oliverpaddock/OpenMic/hardware/sims/output.asc

B1: bv; V=white(2.8e6*time)*0.0038
B2: bv; V=white(45e6*time)*0.005
B3: bv; V=white(8.4e6*time)*0.000021
B4: bv; V=white(8.4e6*time)*0.000021
B5: bv; V=white(2e6*time)*0.000002
C1: Cap; 47µ
C2: Cap; 100n
C3: Cap; 100n
C4: Cap; 100n
C5: Cap; 100n
C6: Cap; 47µ
R1: Res; 10
R2: Res; 1k
R3: Res; 5k1
R4: Res; 1k
R5: Res; 10
R6: Res; 1k
R8: Res; 6.34k
R9: Res; 6.34k
R11: Res; 1k
U1: opamp2; OPA161x
U2: OPA1637
V1: Voltage; 48
V2: Voltage; SINE(0 3.8m 700k 0 0 0)
V3: Voltage; 3.3
V4: Voltage; SINE(0 5m 2.25meg)
V5: Voltage; 15.2
V6: Voltage; SINE(0 5m 420k)
V7: Voltage; -15.1
V8: Voltage; SINE(0 5m 420k)
V9: Voltage; 2.75
V10: Voltage; SINE(1.65 .5 440); AC 1; Cpar=2n
V11: Voltage; SINE(1.65 .5 440); AC 1; Cpar=2n
Named nets: 0, +48V_PH, +3V3, +15V, -15V, +2V75_BIAS
.lib ./models/OPA161x.lib
.lib ./models/OPA1622.lib
.lib ./models/OPA1637.lib
.lib ./models/OPA164x.lib
.lib ./models/OPA1656.lib
.lib ./models/THAT120x.lib
.lib ./models/THAT1580.lib
.lib ./models/THAT5173.lib
.tran 0 5m
