oliverpaddock/OpenMic/hardware/pcb/prototypes/input/v1/input.kicad_pcb

## KiCad design hardware/pcb/prototypes/input/v1/input.kicad_pcb (2026-06-01, an earlier design)

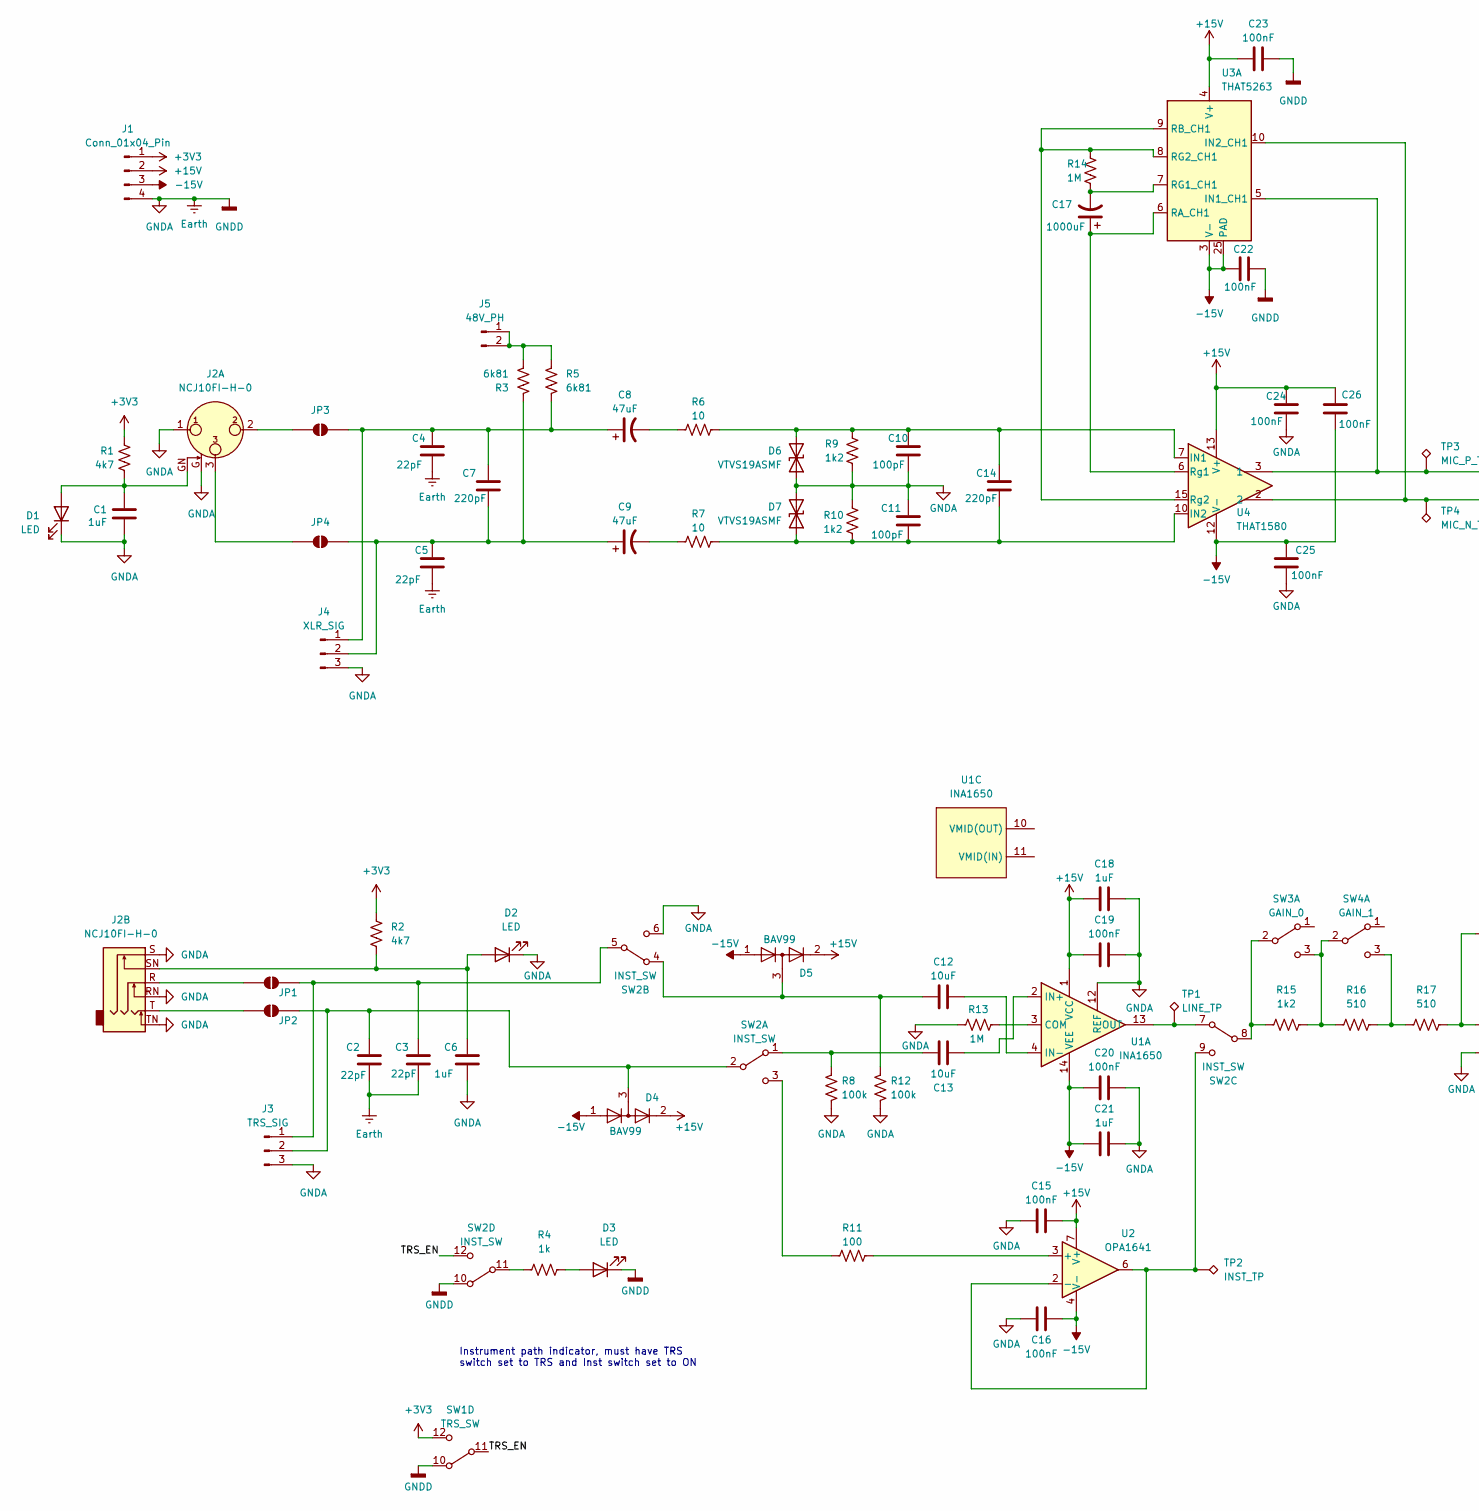
[picture p43: schematic input.kicad_sch, Audio input test, part in row 1, column 1]

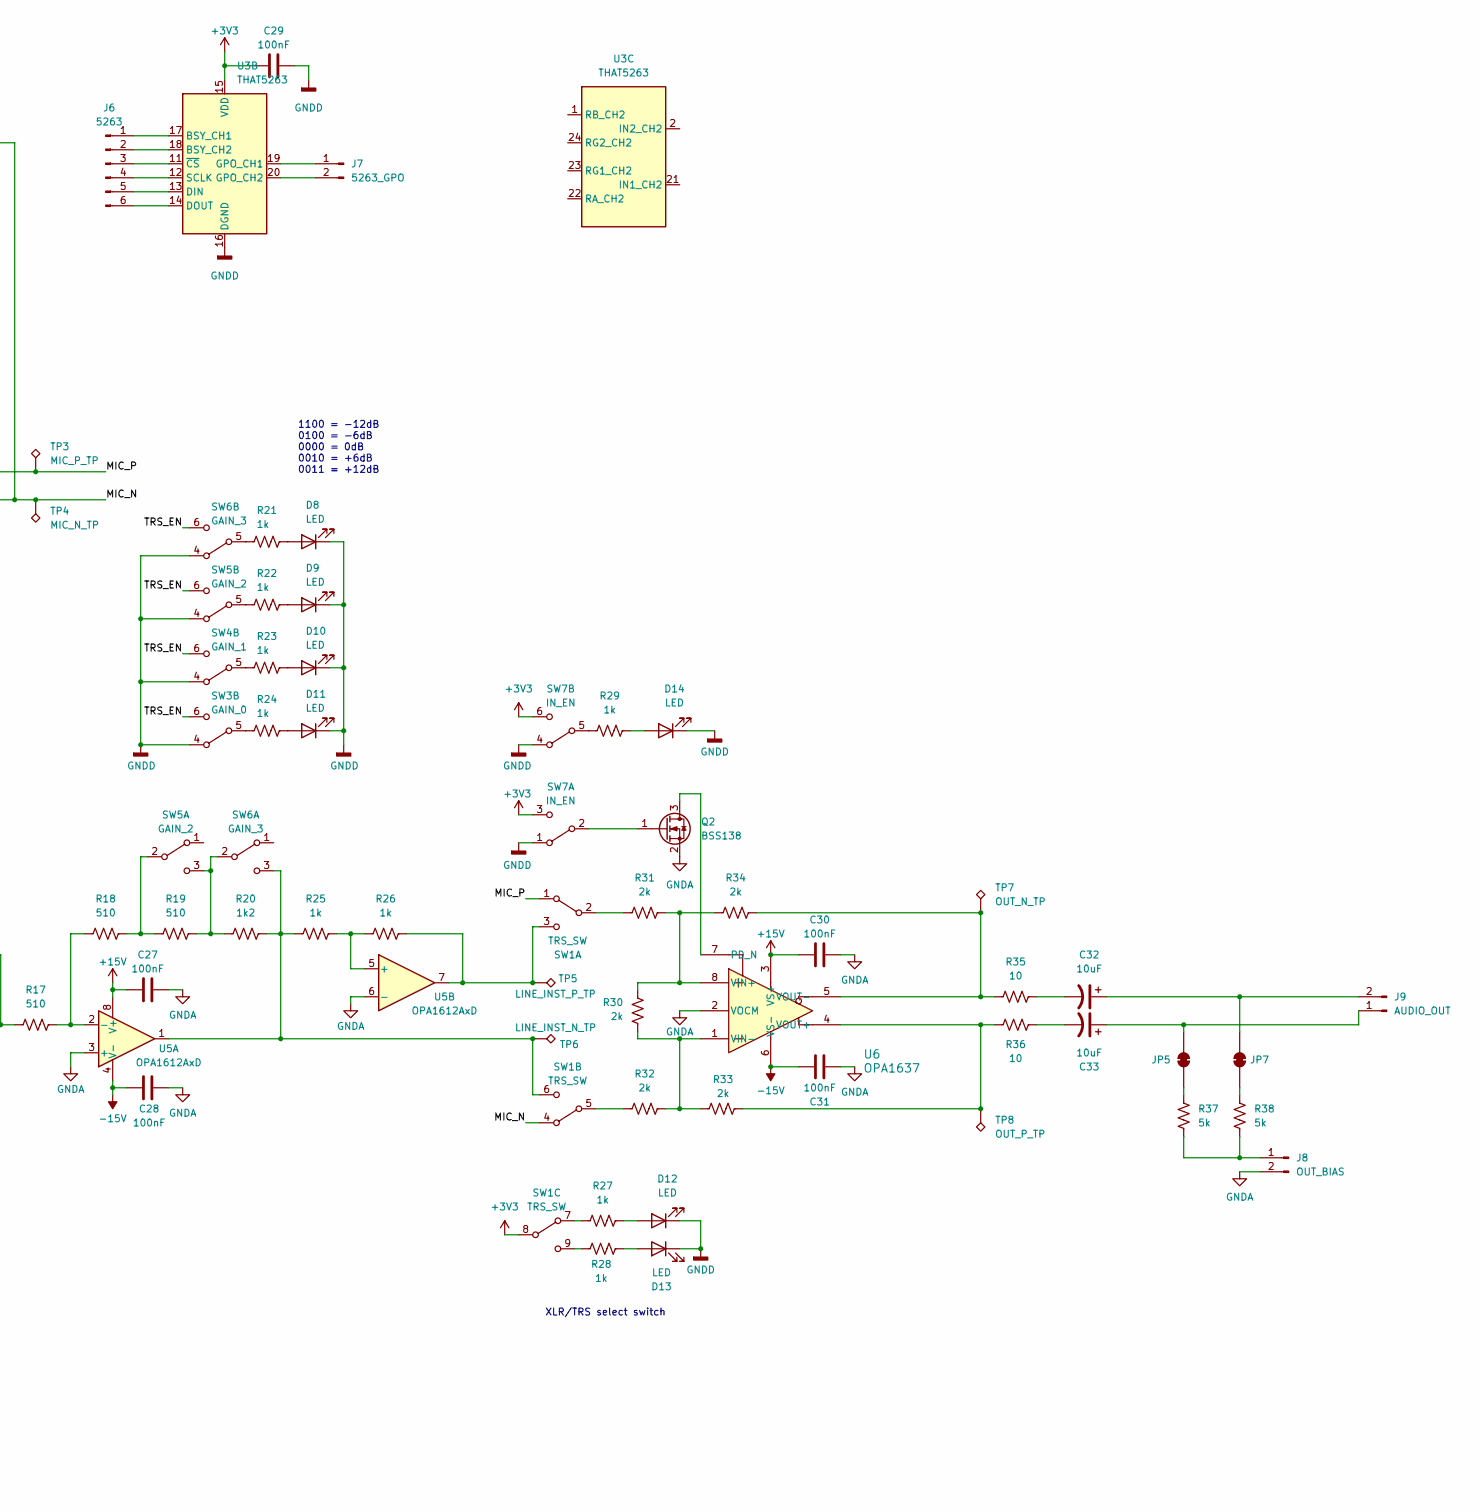
[picture p44: schematic input.kicad_sch, Audio input test, part in row 1, column 2]

Parts:
C1, C6, C18, C21: 1uF; C_0805_2012Metric_Pad1.18x1.45mm_HandSolder
C2, C3, C4, C5: 22pF; C_0805_2012Metric_Pad1.18x1.45mm_HandSolder
C7, C14: 220pF; C_0805_2012Metric_Pad1.18x1.45mm_HandSolder
C8, C9: 47uF; CP_Elec_6.3x5.8
C10, C11: 100pF; C_0805_2012Metric_Pad1.18x1.45mm_HandSolder
C12, C13: 10uF; C_0805_2012Metric_Pad1.18x1.45mm_HandSolder
C15, C16, C19, C20, C22, C23, C24, C25, C26, C27, C28, C29, C30, C31: 100nF; C_0805_2012Metric_Pad1.18x1.45mm_HandSolder
C17: 1000uF; CP_Elec_8x10
C32, C33: 10uF; CP_Elec_5x5.4
D1, D2, D3, D8, D9, D10, D11, D12, D13, D14: LED; LED_0805_2012Metric_Pad1.15x1.40mm_HandSolder
D4, D5: BAV99; TSOT-23_HandSoldering
D6, D7: VTVS19ASMF; D_SMF
J1: Conn_01x04_Pin; PinHeader_1x04_P2.54mm_Vertical
J2: NCJ10FI-H-0; Jack_XLR-6.35mm_Neutrik_NCJ10FI-H-0_Horizontal
J3: TRS_SIG; PinHeader_1x03_P2.54mm_Vertical
J4: XLR_SIG; PinHeader_1x03_P2.54mm_Vertical
J5: 48V_PH; PinHeader_1x02_P2.54mm_Vertical
J6: 5263; PinHeader_1x06_P2.54mm_Vertical
J7: 5263_GPO; PinHeader_1x02_P2.54mm_Vertical
J8: OUT_BIAS; PinHeader_1x02_P2.54mm_Vertical
J9: AUDIO_OUT; PinHeader_1x02_P2.54mm_Vertical
JP1, JP2, JP3, JP4: SolderJumper_2_Open; SolderJumper-2_P1.3mm_Open_RoundedPad1.0x1.5mm
JP5, JP7: SolderJumper_2_Bridged; SolderJumper-2_P1.3mm_Bridged2Bar_RoundedPad1.0x1.5mm
Q2: BSS138; SOT-23
R1, R2: 4k7; R_0805_2012Metric_Pad1.20x1.40mm_HandSolder
R3, R5: 6k81; R_0805_2012Metric_Pad1.20x1.40mm_HandSolder
R4, R21, R22, R23, R24, R25, R26, R27, R28, R29: 1k; R_0805_2012Metric_Pad1.20x1.40mm_HandSolder
R6, R7, R35, R36: 10; R_0805_2012Metric_Pad1.20x1.40mm_HandSolder
R8, R12: 100k; R_0805_2012Metric_Pad1.20x1.40mm_HandSolder
R9, R10, R15, R20: 1k2; R_0805_2012Metric_Pad1.20x1.40mm_HandSolder
R11: 100; R_0805_2012Metric_Pad1.20x1.40mm_HandSolder
R13, R14: 1M; R_0805_2012Metric_Pad1.20x1.40mm_HandSolder
R16, R17, R18, R19: 510; R_0805_2012Metric_Pad1.20x1.40mm_HandSolder
R30, R31, R32, R33, R34: 2k; R_0805_2012Metric_Pad1.20x1.40mm_HandSolder
R37, R38: 5k; R_0805_2012Metric_Pad1.20x1.40mm_HandSolder
SW1: TRS_SW; 4PDT_SW
SW2: INST_SW; 4PDT_SW
SW3: GAIN_0; DPDT_SW
SW4: GAIN_1; DPDT_SW
SW5: GAIN_2; DPDT_SW
SW6: GAIN_3; DPDT_SW
SW7: IN_EN; DPDT_SW
TP1: LINE_TP; TestPoint_Pad_D1.0mm
TP2: INST_TP; TestPoint_Pad_D1.0mm
TP3: MIC_P_TP; TestPoint_Pad_D1.0mm
TP4: MIC_N_TP; TestPoint_Pad_D1.0mm
TP5: LINE_INST_P_TP; TestPoint_Pad_D1.0mm
TP6: LINE_INST_N_TP; TestPoint_Pad_D1.0mm
TP7: OUT_N_TP; TestPoint_Pad_D1.0mm
TP8: OUT_P_TP; TestPoint_Pad_D1.0mm
U1: INA1650; TSSOP-14_4.4x5mm_P0.65mm
U2: OPA1641; SOIC-8_3.9x4.9mm_P1.27mm
U3: THAT5263; QFN-24-1EP_5x5mm_P0.65mm_EP3.4x3.4mm
U4: THAT1580; QFN-16-1EP_4x4mm_P0.65mm_EP2.1x2.1mm_ThermalVias
U5: OPA1612AxD; SOIC-8_3.9x4.9mm_P1.27mm
U6: OPA1637; VSSOP-8_3x3mm_P0.65mm

Connections:
+3V3: C29.1, J1.1, R1.1, R2.1, SW1.8 (B), SW1.12 (C), SW7.3 (C), SW7.6 (C), U3.15 (VDD)
+15V: C15.1, C18.2, C19.2, C23.1, C24.1, C26.1, C27.1, C30.1, D4.2 (A), D5.2 (A), J1.2, U1.1 (VCC), U2.7 (V+), U3.4 (V+), U4.13 (V+), U5.8 (V+), U6.3 (VS+)
-15V: C16.1, C20.1, C21.2, C22.1, C25.1, C26.2, C28.1, C31.1, D4.1 (K), D5.1 (K), J1.3, U1.14 (VEE), U2.4 (V-), U3.3 (V-), U3.25 (PAD), U4.12 (V-), U4.17 (V-), U5.4 (V-), U6.6 (VS-)
/MIC_N: SW1.4 (A), TP4.1 (1_1), U3.10 (IN2_CH1), U4.2
/MIC_P: SW1.1 (A), TP3.1 (1_1), U3.5 (IN1_CH1), U4.3 (1)
/TRS_EN: SW1.11 (B), SW2.12 (C), SW3.6 (C), SW4.6 (C), SW5.6 (C), SW6.6 (C)
Earth: C1.2, C2.2, C3.2, C4.2, C5.2, C6.2, C10.2, C11.1, C15.2, C16.2, C18.1, C19.1, C20.2, C21.1, C22.2, C23.2, C24.2, C25.2, C27.2, C28.2, C29.2, C30.2, C31.2, D1.1 (K), D2.1 (K), D3.1 (K), D6.1 (A1), D7.2 (A2), D8.1 (K), D9.1 (K), D10.1 (K), D11.1 (K), D12.1 (K), D13.1 (K), D14.1 (K), J1.4, J2.1, J2.G, J2.RN, J2.S, J2.TN, J3.3, J4.3, J8.2, Q2.2 (S), R8.2, R9.2, R10.1, R12.2, R13.1, SW1.10 (A), SW2.6 (C), SW2.10 (A), SW3.4 (A), SW4.4 (A), SW5.4 (A), SW6.4 (A), SW7.1 (A), SW7.4 (A), U1.12 (REF), U3.16 (DGND), U5.3 (+), U5.6 (-), U6.2 (VOCM)
unnamed: C8.2, R6.1
unnamed: C9.2, R7.1
unnamed: C32.2, R35.2
unnamed: C33.2, R36.2
unnamed: C1.1, D1.2 (A), J2.GN, R1.2
unnamed: C6.1, D2.2 (A), J2.SN, R2.2
unnamed: D3.2 (A), R4.2
unnamed: C10.1, C14.1, D6.2 (A2), R6.2, R9.1, U4.7 (IN1)
unnamed: C11.2, C14.2, D7.1 (A1), R7.2, R10.2, U4.10 (IN2)
unnamed: D8.2 (A), R21.1
unnamed: D9.2 (A), R22.1
unnamed: D10.2 (A), R23.1
unnamed: D11.2 (A), R24.1
unnamed: D12.2 (A), R27.2
unnamed: D13.2 (A), R28.2
unnamed: D14.2 (A), R29.2
unnamed: C3.1, J3.1, JP1.2 (B), SW2.5 (B)
unnamed: C2.1, D4.3 (K), J3.2, JP2.2 (B), SW2.2 (B)
unnamed: C4.1, C7.1, C8.1, J4.1, JP3.2 (B), R5.2
unnamed: C5.1, C7.2, C9.1, J4.2, JP4.2 (B), R3.1
unnamed: J5.1, J5.2, R3.2, R5.1
unnamed: J6.1, U3.17 (BSY_CH1)
unnamed: J6.2, U3.18 (BSY_CH2)
unnamed: J6.3, U3.11 (~CS)
unnamed: J6.4, U3.12 (SCLK)
unnamed: J6.5, U3.13 (DIN)
unnamed: J6.6, U3.14 (DOUT)
unnamed: J7.1, U3.19 (GPO_CH1)
unnamed: J7.2, U3.20 (GPO_CH2)
unnamed: J8.1, R37.1, R38.1
unnamed: C33.1, J9.1, JP5.2 (B)
unnamed: C32.1, J9.2, JP7.2 (B)
unnamed: J2.R, JP1.1 (A)
unnamed: J2.T, JP2.1 (A)
unnamed: J2.2, JP3.1 (A)
unnamed: J2.3, JP4.1 (A)
unnamed: JP5.1 (A), R37.2
unnamed: JP7.1 (A), R38.2
unnamed: Q2.3 (D), U6.7 (PD_N)
unnamed: Q2.1 (G), SW7.2 (B)
unnamed: R31.1, SW1.2 (B)
unnamed: R26.2, SW1.3 (C), TP5.1 (1_1), U5.7
unnamed: R32.1, SW1.5 (B)
unnamed: R20.2, R25.1, SW1.6 (C), SW6.3 (C), TP6.1 (1_1), U5.1
unnamed: R27.1, SW1.7 (A)
unnamed: R28.1, SW1.9 (C)
unnamed: C13.2, R8.1, SW2.1 (A)
unnamed: R11.1, SW2.3 (C)
unnamed: C12.2, D5.3 (K), R12.1, SW2.4 (A)
unnamed: SW2.7 (A), TP1.1 (1_1), U1.13 (OUT)
unnamed: R15.1, SW2.8 (B), SW3.2 (B)
unnamed: SW2.9 (C), TP2.1 (1_1), U2.2 (-), U2.6
unnamed: R4.1, SW2.11 (B)
unnamed: R15.2, R16.1, SW3.3 (C), SW4.2 (B)
unnamed: R24.2, SW3.5 (B)
unnamed: R16.2, R17.1, SW4.3 (C)
unnamed: R23.2, SW4.5 (B)
unnamed: R18.2, R19.1, SW5.2 (B)
unnamed: R19.2, R20.1, SW5.3 (C), SW6.2 (B)
unnamed: R22.2, SW5.5 (B)
unnamed: R21.2, SW6.5 (B)
unnamed: R29.1, SW7.5 (B)
unnamed: R13.2, U1.3 (COM)
unnamed: C13.1, U1.2 (IN+)
unnamed: C12.1, U1.4 (IN-)
unnamed: R11.2, U2.3 (+)
unnamed: C17.1, U3.6 (RA_CH1), U4.6 (Rg1)
unnamed: R14.1, U3.8 (RG2_CH1), U3.9 (RB_CH1), U4.15 (Rg2)
unnamed: C17.2, R14.2, U3.7 (RG1_CH1)
unnamed: R17.2, R18.1, U5.2 (-)
unnamed: R25.2, R26.1, U5.5 (+)
unnamed: R30.2, R31.2, R34.1, U6.8 (VIN+)
unnamed: R30.1, R32.2, R33.2, U6.1 (VIN-)
unnamed: R33.1, R36.1, TP8.1 (1_1), U6.4 (VOUT+)
unnamed: R34.2, R35.1, TP7.1 (1_1), U6.5 (VOUT-)

Notes on the sheet:
XLR/TRS select switch
Instrument path indicator, must have TRS switch set to TRS and Inst switch set to ON
1100 = -12dB 0100 = -6dB 0000 = 0dB 0010 = +6dB 0011 = +12dB

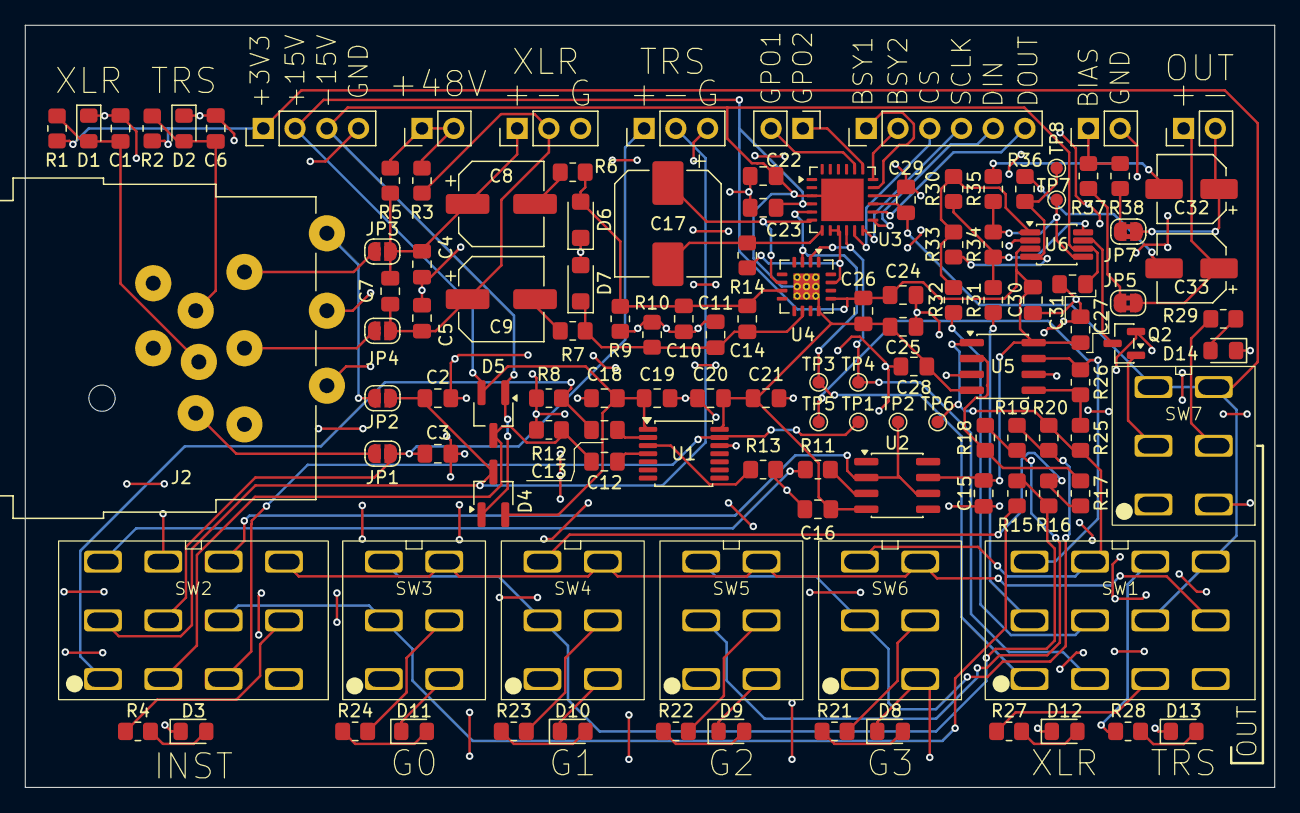
[picture p45: board input.kicad_pcb from above]

Board: 2 copper layers, 100.0 x 61.0 mm, 122 parts (0 on the bottom side), 82 nets.
