oliverpaddock/OpenMic/hardware/pcb/main-board/openmic.kicad_pcb

## KiCad design hardware/pcb/main-board/openmic.kicad_pcb (2026-07-04)

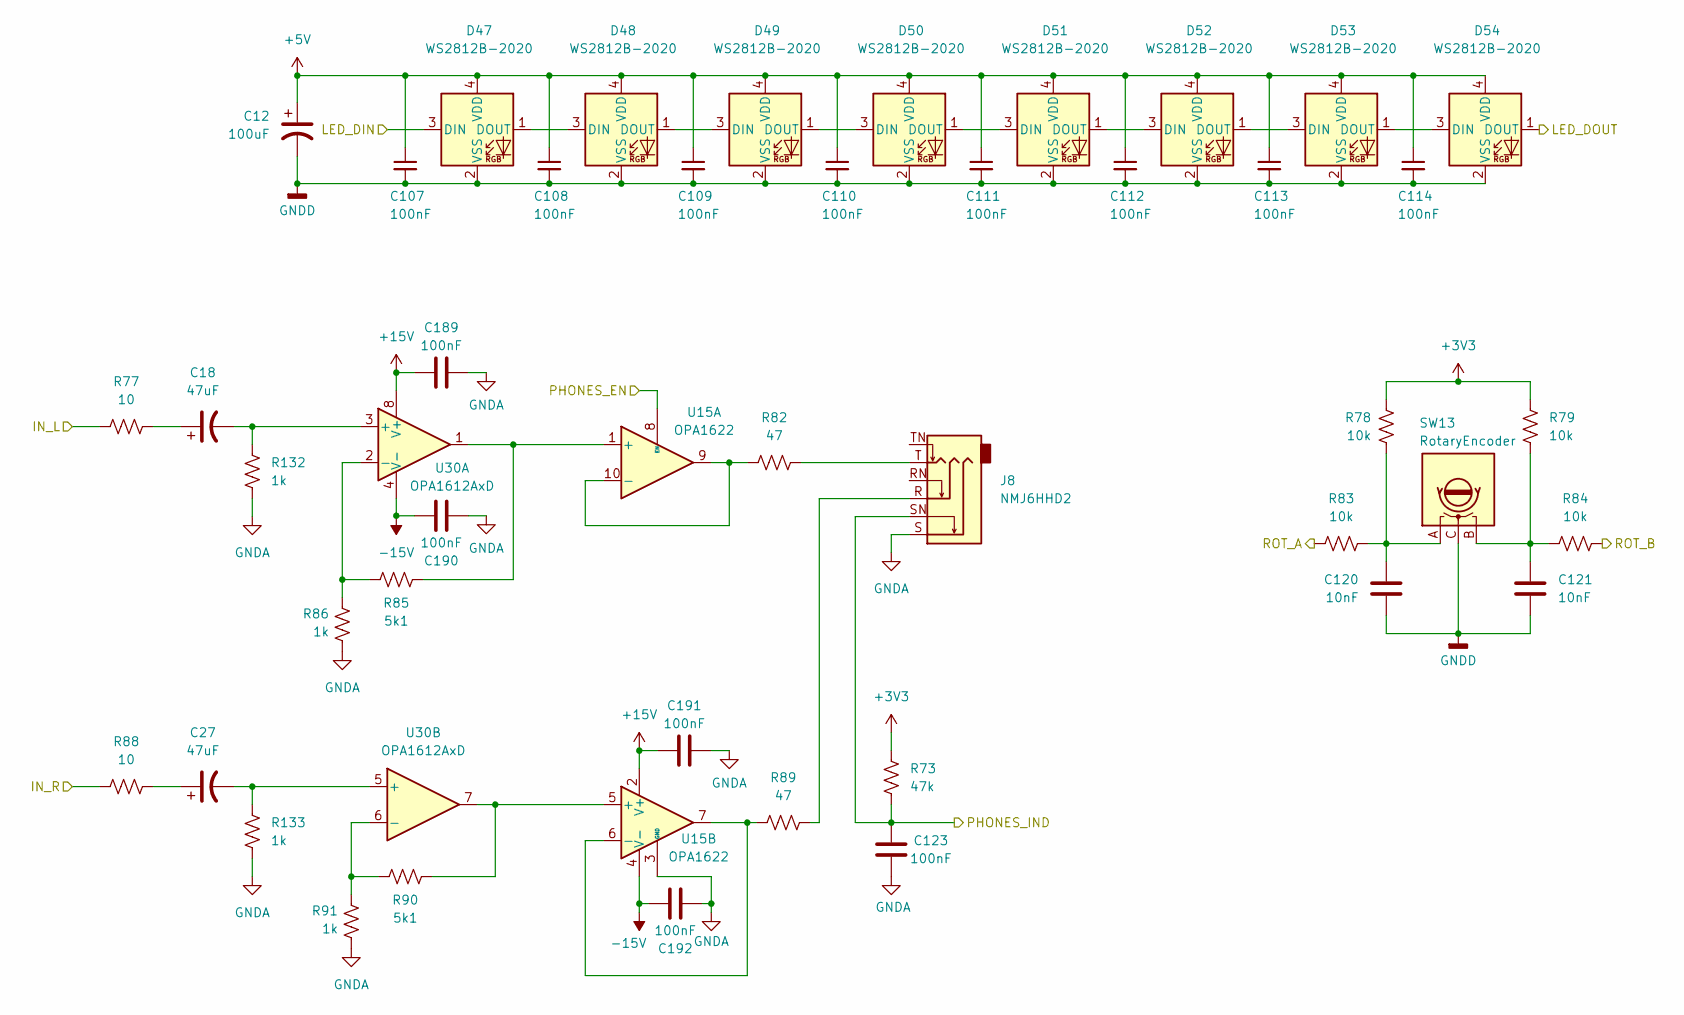
[picture p46: schematic phones.kicad_sch, Headphones out]

Parts:
C12: 100uF; CP_Elec_6.3x5.4
C18, C27: 47uF; CP_Elec_6.3x5.4
C107, C108, C109, C110, C111, C112, C113, C114, C123, C189, C190, C191, C192: 100nF; C_0603_1608Metric_Pad1.08x0.95mm_HandSolder
C120, C121: 10nF; C_0603_1608Metric_Pad1.08x0.95mm_HandSolder
D47, D48, D49, D50, D51, D52, D53, D54: WS2812B-2020; LED_WS2812B-2020_PLCC4_2.0x2.0mm
J8: NMJ6HHD2; Jack_6.35mm_Neutrik_NMJ6HHD2_Horizontal
R73: 47k; R_0603_1608Metric_Pad0.98x0.95mm_HandSolder
R77, R88: 10; R_0603_1608Metric_Pad0.98x0.95mm_HandSolder
R78, R79, R83, R84: 10k; R_0603_1608Metric_Pad0.98x0.95mm_HandSolder
R82, R89: 47; R_0603_1608Metric_Pad0.98x0.95mm_HandSolder
R85, R90: 5k1; R_0603_1608Metric_Pad0.98x0.95mm_HandSolder
R86, R91, R132, R133: 1k; R_0603_1608Metric_Pad0.98x0.95mm_HandSolder
SW13: RotaryEncoder; PEC11L
U15: OPA1622; Texas_S-PVSON-N10
U30: OPA1612AxD; SOIC-8_3.9x4.9mm_P1.27mm

Connections:
+3V3: R73.1, R78.2, R79.1; also elsewhere on the board
+5V: C12.1, C107.1, C108.1, C109.1, C110.1, C111.1, C112.1, C113.1, C114.1, D47.4 (VDD), D48.4 (VDD), D49.4 (VDD), D50.4 (VDD), D51.4 (VDD), D52.4 (VDD), D53.4 (VDD), D54.4 (VDD); also elsewhere on the board
+15V: C189.1, C191.1, U15.2 (V+), U30.8 (V+); also elsewhere on the board
-15V: C190.1, C192.1, U15.4 (V-), U15.11 (V-), U30.4 (V-); also elsewhere on the board
/codec/OUT_PHONE_L: R77.1; also elsewhere on the board
/codec/OUT_PHONE_R: R88.1; also elsewhere on the board
/input/LED_2_DOUT: D47.3 (DIN); also elsewhere on the board
/line driver/LED_DIN: D54.1 (DOUT); also elsewhere on the board
/usb bridge/GP0_8C_4: U15.8 (EN); also elsewhere on the board
/usb bridge/GP0_8D_4: C123.1, J8.SN, R73.2; also elsewhere on the board
/usb bridge/GP1_1L: R83.1; also elsewhere on the board
/usb bridge/GP1_1M: R84.2; also elsewhere on the board
Earth: C12.2, C107.2, C108.2, C109.2, C110.2, C111.2, C112.2, C113.2, C114.2, C120.2, C121.2, C123.2, C189.2, C190.2, C191.2, C192.2, D47.2 (VSS), D48.2 (VSS), D49.2 (VSS), D50.2 (VSS), D51.2 (VSS), D52.2 (VSS), D53.2 (VSS), D54.2 (VSS), J8.S, R86.2, R91.2, R132.1, R133.1, SW13.C, U15.3 (GND); also elsewhere on the board
unnamed: C18.1, R77.2
unnamed: C27.1, R88.2
unnamed: C120.1, R78.1, R83.2, SW13.A
unnamed: C121.1, R79.2, R84.1, SW13.B
unnamed: D47.1 (DOUT), D48.3 (DIN)
unnamed: D48.1 (DOUT), D49.3 (DIN)
unnamed: D49.1 (DOUT), D50.3 (DIN)
unnamed: D50.1 (DOUT), D51.3 (DIN)
unnamed: D51.1 (DOUT), D52.3 (DIN)
unnamed: D52.1 (DOUT), D53.3 (DIN)
unnamed: D53.1 (DOUT), D54.3 (DIN)
unnamed: J8.R, R89.2
unnamed: J8.T, R82.2
unnamed: R85.1, U15.1 (+), U30.1
unnamed: R82.1, U15.9, U15.10 (-)
unnamed: R90.1, U15.5 (+), U30.7
unnamed: R89.1, U15.6 (-), U15.7
unnamed: C18.2, R132.2, U30.3 (+)
unnamed: R85.2, R86.1, U30.2 (-)
unnamed: C27.2, R133.2, U30.5 (+)
unnamed: R90.2, R91.1, U30.6 (-)
