oliverpaddock/OpenMic/hardware/pcb/main-board/openmic.kicad_pcb

## KiCad design hardware/pcb/main-board/openmic.kicad_pcb (continued)

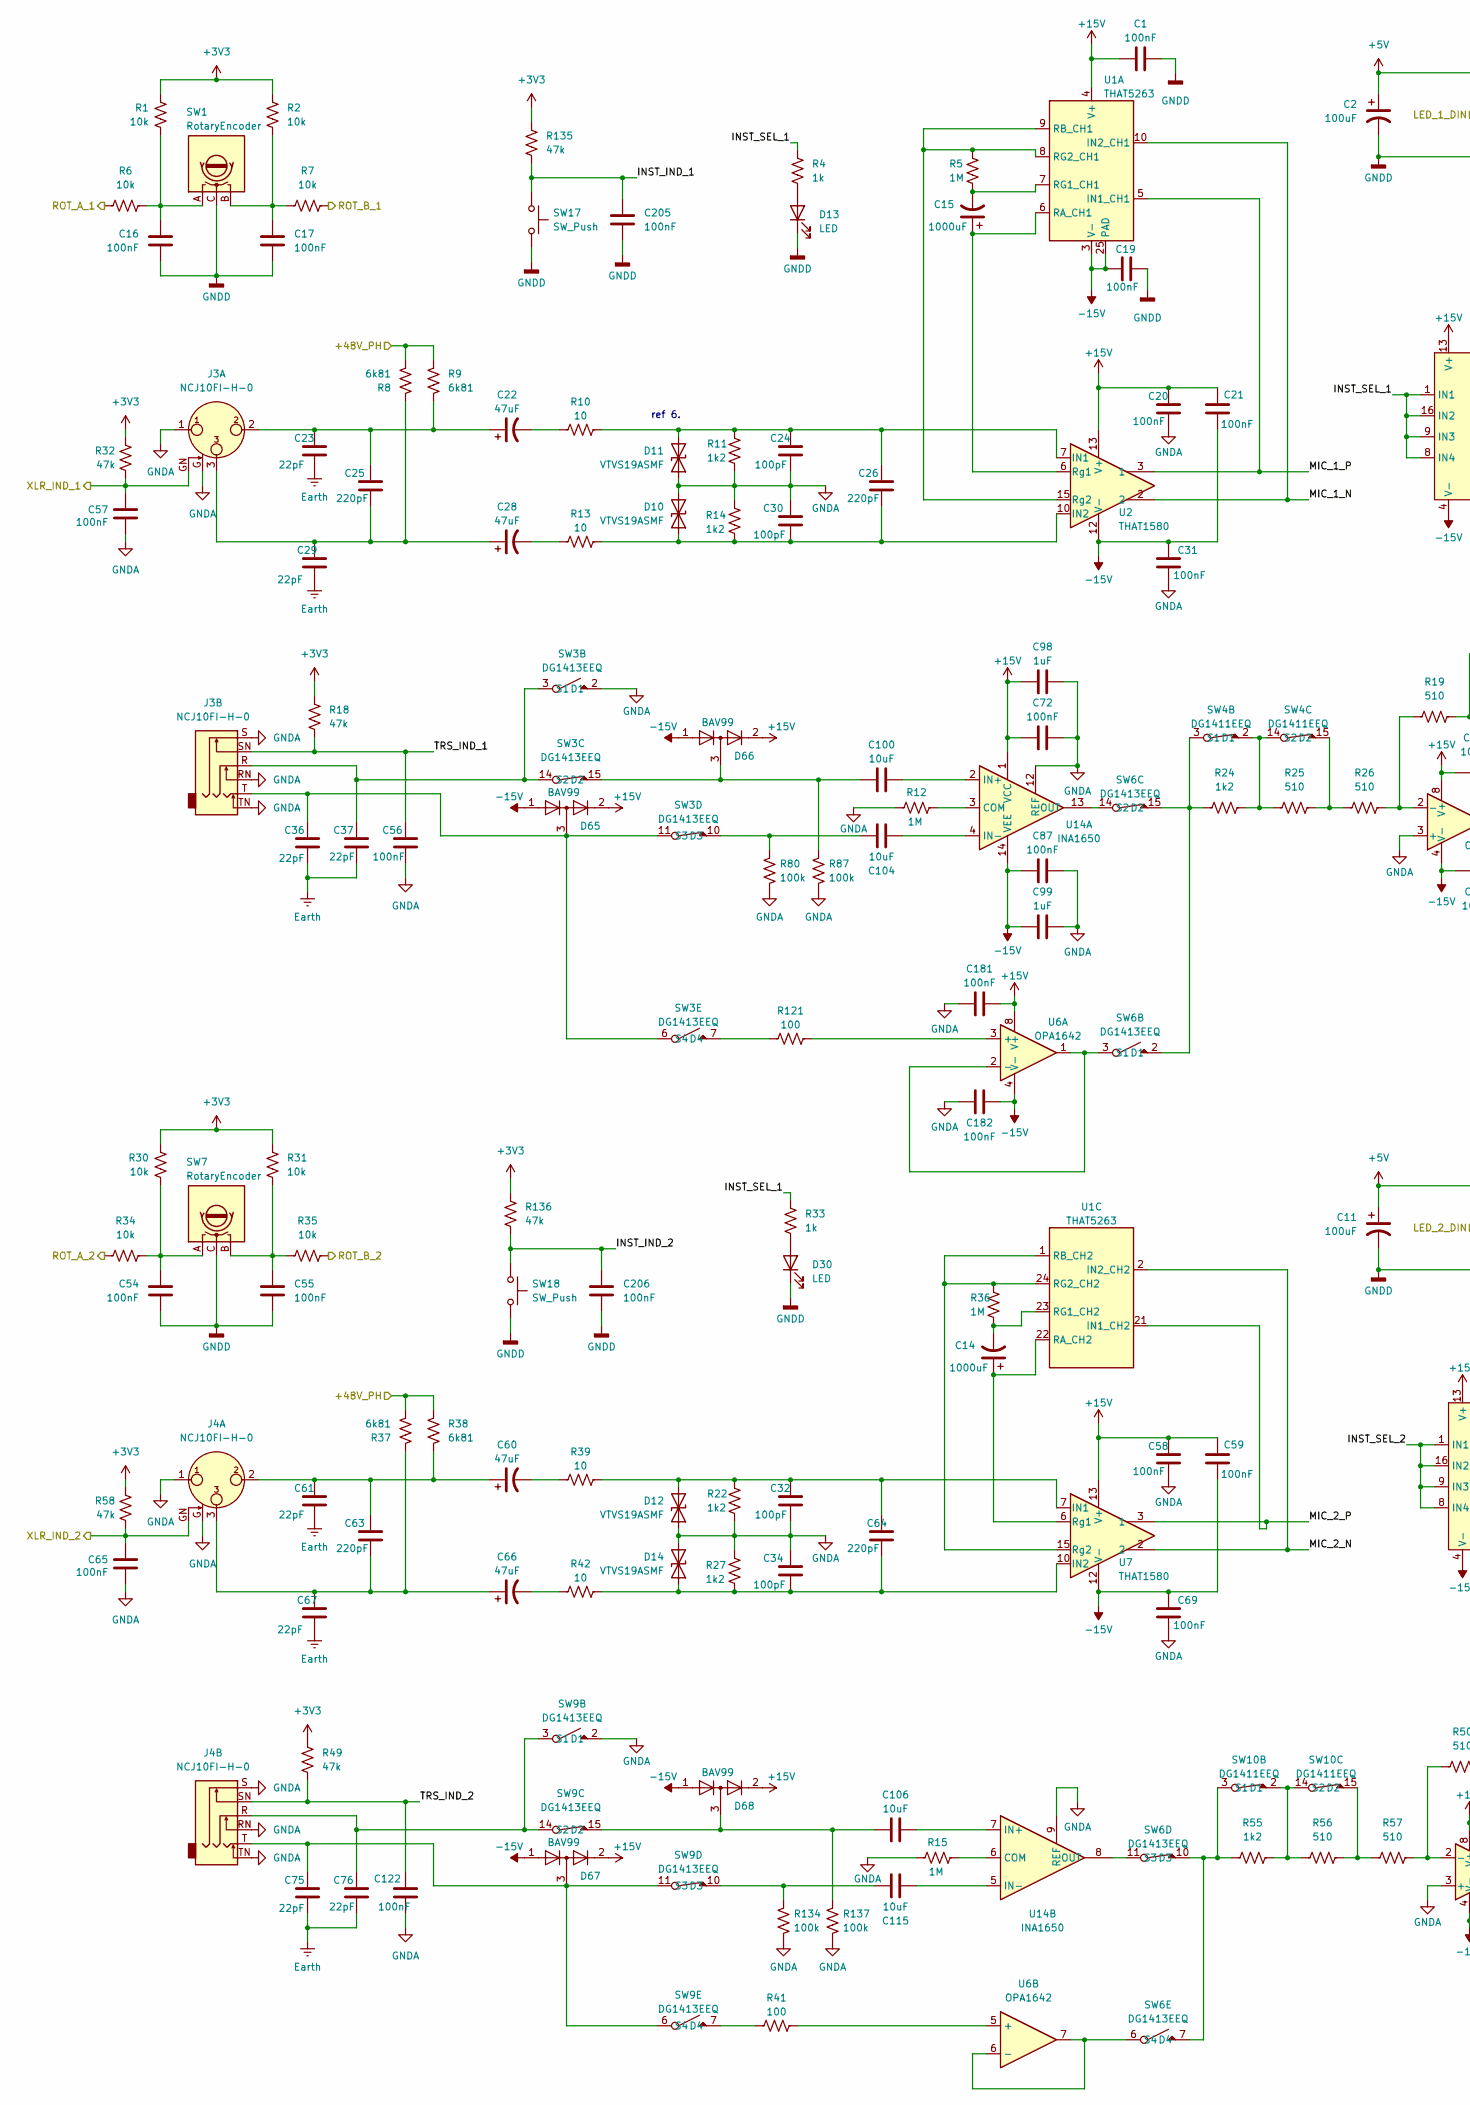
[picture p47: schematic input.kicad_sch, Audio inputs, part in row 1, column 1]

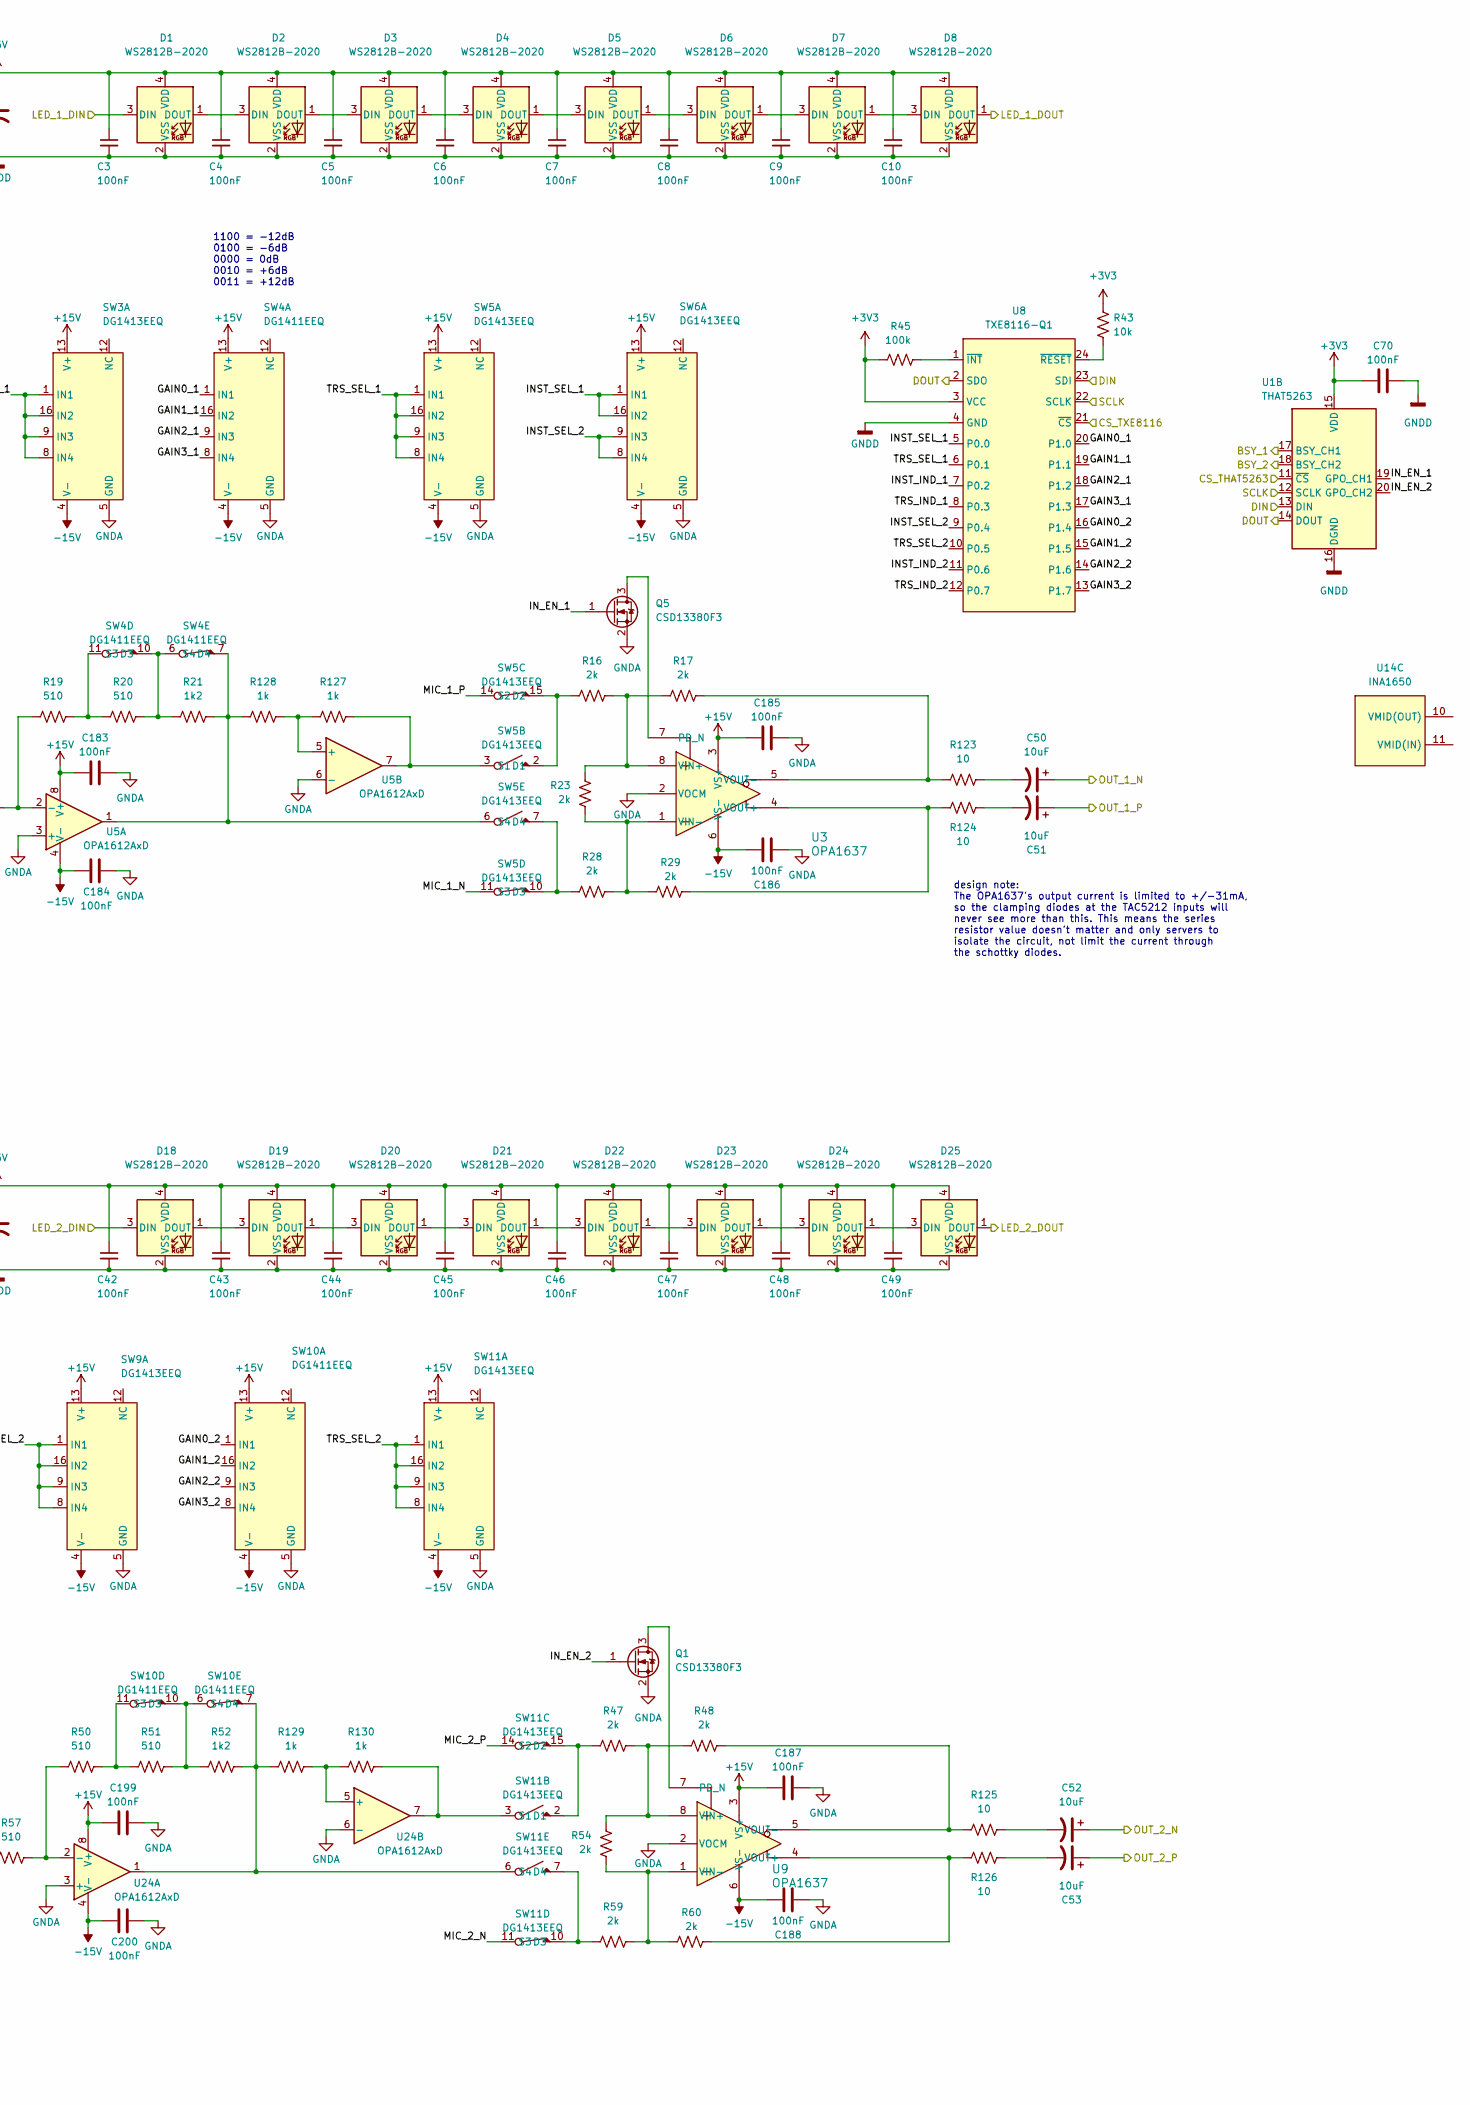
[picture p48: schematic input.kicad_sch, Audio inputs, part in row 1, column 2]

Parts:
C1, C3, C4, C5, C6, C7, C8, C9, C10, C16, C17, C19, C20, C21, C31, C42, C43, C44, C45, C46, C47, C48, C49, C54, C55, C56, C57, C58, C59, C65, C69, C70, C72, C87, C122, C181, C182, C183, C184, C185, C186, C187, C188, C199, C200, C205, C206: 100nF; C_0603_1608Metric_Pad1.08x0.95mm_HandSolder
C2, C11: 100uF; CP_Elec_6.3x5.4
C14, C15: 1000uF; CP_Elec_8x10.5
C22, C28, C60, C66: 47uF; CP_Elec_6.3x5.4
C23, C29, C36, C37, C61, C67, C75, C76: 22pF; C_0603_1608Metric_Pad1.08x0.95mm_HandSolder
C24, C30, C32, C34: 100pF; C_0603_1608Metric_Pad1.08x0.95mm_HandSolder
C25, C26, C63, C64: 220pF; C_0603_1608Metric_Pad1.08x0.95mm_HandSolder
C50, C51, C52, C53: 10uF; CP_Elec_6.3x5.4
C98, C99: 1uF; C_0603_1608Metric_Pad1.08x0.95mm_HandSolder
C100, C104, C106, C115: 10uF; C_0603_1608Metric_Pad1.08x0.95mm_HandSolder
D1, D2, D3, D4, D5, D6, D7, D8, D18, D19, D20, D21, D22, D23, D24, D25: WS2812B-2020; LED_WS2812B-2020_PLCC4_2.0x2.0mm
D10, D11, D12, D14: VTVS19ASMF
D13, D30: LED; LED_0603_1608Metric_Pad1.05x0.95mm_HandSolder
D65, D66, D67, D68: BAV99; SOT-23
J3, J4: NCJ10FI-H-0; Jack_XLR-6.35mm_Neutrik_NCJ10FI-H-0_Horizontal
Q1, Q5: CSD13380F3; Texas_PicoStar_DFN-3_0.69x0.60mm
R1, R2, R6, R7, R30, R31, R34, R35, R43: 10k; R_0603_1608Metric_Pad0.98x0.95mm_HandSolder
R4, R33, R127, R128, R129, R130: 1k; R_0603_1608Metric_Pad0.98x0.95mm_HandSolder
R5, R12, R15, R36: 1M; R_0603_1608Metric_Pad0.98x0.95mm_HandSolder
R8, R9, R37, R38: 6k81; R_0603_1608Metric_Pad0.98x0.95mm_HandSolder
R10, R13, R39, R42, R123, R124, R125, R126: 10; R_0603_1608Metric_Pad0.98x0.95mm_HandSolder
R11, R14, R21, R22, R24, R27, R52, R55: 1k2; R_0603_1608Metric_Pad0.98x0.95mm_HandSolder
R16, R17, R23, R28, R29, R47, R48, R54, R59, R60: 2k; R_0603_1608Metric_Pad0.98x0.95mm_HandSolder
R18, R32, R49, R58, R135, R136: 47k; R_0603_1608Metric_Pad0.98x0.95mm_HandSolder
R19, R20, R25, R26, R50, R51, R56, R57: 510; R_0603_1608Metric_Pad0.98x0.95mm_HandSolder
R41, R121: 100; R_0603_1608Metric_Pad0.98x0.95mm_HandSolder
R45, R80, R87, R134, R137: 100k; R_0603_1608Metric_Pad0.98x0.95mm_HandSolder
SW1, SW7: RotaryEncoder; PEC11L
SW3, SW5, SW6, SW9, SW11: DG1413EEQ; TSSOP-16_4.4x5mm_P0.65mm
SW4, SW10: DG1411EEQ; TSSOP-16_4.4x5mm_P0.65mm
SW17, SW18: SW_Push; SW_Push_1P1T_XKB_TS-1187A
U1: THAT5263; QFN-24-1EP_5x5mm_P0.65mm_EP3.4x3.4mm
U2, U7: THAT1580; QFN-16-1EP_4x4mm_P0.65mm_EP2.1x2.1mm_ThermalVias
U3, U9: OPA1637; VSSOP-8_3x3mm_P0.65mm
U5, U24: OPA1612AxD; SOIC-8_3.9x4.9mm_P1.27mm
U6: OPA1642; VSSOP-8_3x3mm_P0.65mm
U8: TXE8116-Q1; VSSOP-24
U14: INA1650; TSSOP-14_4.4x5mm_P0.65mm

Connections:
+3V3: C70.1, R1.2, R2.1, R18.1, R30.2, R31.1, R32.1, R43.2, R45.2, R49.1, R58.1, R135.1, R136.1, U1.15 (VDD), U8.3 (VCC); also elsewhere on the board
+5V: C2.1, C3.1, C4.1, C5.1, C6.1, C7.1, C8.1, C9.1, C10.1, C11.1, C42.1, C43.1, C44.1, C45.1, C46.1, C47.1, C48.1, C49.1, D1.4 (VDD), D2.4 (VDD), D3.4 (VDD), D4.4 (VDD), D5.4 (VDD), D6.4 (VDD), D7.4 (VDD), D8.4 (VDD), D18.4 (VDD), D19.4 (VDD), D20.4 (VDD), D21.4 (VDD), D22.4 (VDD), D23.4 (VDD), D24.4 (VDD), D25.4 (VDD); also elsewhere on the board
+15V: C1.1, C20.1, C21.1, C58.1, C59.1, C72.2, C98.2, C181.1, C183.1, C185.1, C187.1, C199.1, D65.2 (A), D66.2 (A), D67.2 (A), D68.2 (A), SW3.13 (V+), SW4.13 (V+), SW5.13 (V+), SW6.13 (V+), SW9.13 (V+), SW10.13 (V+), SW11.13 (V+), U1.4 (V+), U2.13 (V+), U3.3 (VS+), U5.8 (V+), U6.8 (V+), U7.13 (V+), U9.3 (VS+), U14.1 (VCC), U24.8 (V+); also elsewhere on the board
-15V: C19.1, C21.2, C31.1, C59.2, C69.1, C87.1, C99.2, C182.1, C184.1, C186.1, C188.1, C200.1, D65.1 (K), D66.1 (K), D67.1 (K), D68.1 (K), SW3.4 (V-), SW4.4 (V-), SW5.4 (V-), SW6.4 (V-), SW9.4 (V-), SW10.4 (V-), SW11.4 (V-), U1.3 (V-), U1.25 (PAD), U2.12 (V-), U2.17 (V-), U3.6 (VS-), U5.4 (V-), U6.4 (V-), U7.12 (V-), U7.17 (V-), U9.6 (VS-), U14.14 (VEE), U24.4 (V-); also elsewhere on the board
/codec/IN_1_N: C50.1; also elsewhere on the board
/codec/IN_1_P: C51.1; also elsewhere on the board
/codec/IN_2_N: C52.1; also elsewhere on the board
/codec/IN_2_P: C53.1; also elsewhere on the board
/input/+48V_PH: R8.2, R9.1, R37.2, R38.1; also elsewhere on the board
/input/GAIN0_1: SW4.1 (IN1), U8.20 (P1.0)
/input/GAIN0_2: SW10.1 (IN1), U8.16 (P1.4)
/input/GAIN1_1: SW4.16 (IN2), U8.19 (P1.1)
/input/GAIN1_2: SW10.16 (IN2), U8.15 (P1.5)
/input/GAIN2_1: SW4.9 (IN3), U8.18 (P1.2)
/input/GAIN2_2: SW10.9 (IN3), U8.14 (P1.6)
/input/GAIN3_1: SW4.8 (IN4), U8.17 (P1.3)
/input/GAIN3_2: SW10.8 (IN4), U8.13 (P1.7)
/input/INST_IND_1: C205.1, R135.2, SW17.1, U8.7 (P0.2)
/input/INST_IND_2: C206.1, R136.2, SW18.1, U8.11 (P0.6)
/input/INST_SEL_1: R4.1, R33.1, SW3.1 (IN1), SW3.8 (IN4), SW3.9 (IN3), SW3.16 (IN2), SW6.1 (IN1), SW6.16 (IN2), U8.5 (P0.0)
/input/INST_SEL_2: SW6.8 (IN4), SW6.9 (IN3), SW9.1 (IN1), SW9.8 (IN4), SW9.9 (IN3), SW9.16 (IN2), U8.9 (P0.4)
/input/IN_EN_1: Q5.1 (G), U1.19 (GPO_CH1)
/input/IN_EN_2: Q1.1 (G), U1.20 (GPO_CH2)
/input/LED_1_DIN: D1.3 (DIN); also elsewhere on the board
/input/LED_1_DOUT: D8.1 (DOUT), D18.3 (DIN)
/input/LED_2_DOUT: D25.1 (DOUT); also elsewhere on the board
/input/MIC_1_N: SW5.11 (S3), U1.10 (IN2_CH1), U2.2
/input/MIC_1_P: SW5.14 (S2), U1.5 (IN1_CH1), U2.3 (1)
/input/MIC_2_N: SW11.11 (S3), U1.2 (IN2_CH2), U7.2
/input/MIC_2_P: SW11.14 (S2), U1.21 (IN1_CH2), U7.3 (1)
/input/TRS_IND_1: C56.1, J3.SN, R18.2, U8.8 (P0.3)
/input/TRS_IND_2: C122.1, J4.SN, R49.2, U8.12 (P0.7)
/input/TRS_SEL_1: SW5.1 (IN1), SW5.8 (IN4), SW5.9 (IN3), SW5.16 (IN2), U8.6 (P0.1)
/input/TRS_SEL_2: SW11.1 (IN1), SW11.8 (IN4), SW11.9 (IN3), SW11.16 (IN2), U8.10 (P0.5)
/usb bridge/GP0_1D: U1.14 (DOUT), U8.2 (SDO); also elsewhere on the board
/usb bridge/GP0_1I: U1.13 (DIN), U8.23 (SDI); also elsewhere on the board
/usb bridge/GP0_1J: U1.12 (SCLK), U8.22 (SCLK); also elsewhere on the board
/usb bridge/GP0_1K: U1.17 (BSY_CH1); also elsewhere on the board
/usb bridge/GP0_1L: U1.18 (BSY_CH2); also elsewhere on the board
/usb bridge/GP0_4C_0: C57.1, J3.GN, R32.2; also elsewhere on the board
/usb bridge/GP0_4D_0: C65.1, J4.GN, R58.2; also elsewhere on the board
/usb bridge/GP0_8C_0: U1.11 (~CS); also elsewhere on the board
/usb bridge/GP0_8C_1: U8.21 (~CS); also elsewhere on the board
/usb bridge/GP1_1G: R6.1; also elsewhere on the board
/usb bridge/GP1_1I: R34.1; also elsewhere on the board
/usb bridge/GP1_1J: R7.2; also elsewhere on the board
/usb bridge/GP1_1K: R35.2; also elsewhere on the board
Earth: C1.2, C2.2, C3.2, C4.2, C5.2, C6.2, C7.2, C8.2, C9.2, C10.2, C11.2, C16.2, C17.2, C19.2, C20.2, C23.2, C24.2, C29.2, C30.1, C31.2, C32.2, C34.1, C36.2, C37.2, C42.2, C43.2, C44.2, C45.2, C46.2, C47.2, C48.2, C49.2, C54.2, C55.2, C56.2, C57.2, C58.2, C61.2, C65.2, C67.2, C69.2, C70.2, C72.1, C75.2, C76.2, C87.2, C98.1, C99.1, C122.2, C181.2, C182.2, C183.2, C184.2, C185.2, C186.2, C187.2, C188.2, C199.2, C200.2, C205.2, C206.2, D1.2 (VSS), D2.2 (VSS), D3.2 (VSS), D4.2 (VSS), D5.2 (VSS), D6.2 (VSS), D7.2 (VSS), D8.2 (VSS), D10.2 (A2), D11.1 (A1), D12.1 (A1), D13.1 (K), D14.2 (A2), D18.2 (VSS), D19.2 (VSS), D20.2 (VSS), D21.2 (VSS), D22.2 (VSS), D23.2 (VSS), D24.2 (VSS), D25.2 (VSS), D30.1 (K), J3.1, J3.G, J3.RN, J3.S, J3.TN, J4.1, J4.G, J4.RN, J4.S, J4.TN, Q1.2 (S), Q5.2 (S), R11.2, R12.1, R14.1, R15.1, R22.2, R27.1, R80.2, R87.2, R134.2, R137.2, SW1.C, SW3.2 (D1), SW3.5 (GND), SW4.5 (GND), SW5.5 (GND), SW6.5 (GND), SW7.C, SW9.2 (D1), SW9.5 (GND), SW10.5 (GND), SW11.5 (GND), SW17.2, SW18.2, U1.16 (DGND), U3.2 (VOCM), U5.3 (+), U5.6 (-), U8.4 (GND), U9.2 (VOCM), U14.9 (REF), U14.12 (REF), U24.3 (+), U24.6 (-); also elsewhere on the board
unnamed: C16.1, R1.1, R6.2, SW1.A
unnamed: C17.1, R2.2, R7.1, SW1.B
unnamed: C22.1, C23.1, C25.1, J3.2, R9.2
unnamed: C22.2, R10.1
unnamed: C25.2, C28.1, C29.1, J3.3, R8.1
unnamed: C28.2, R13.1
unnamed: C50.2, R123.2
unnamed: C51.2, R124.2
unnamed: C52.2, R125.2
unnamed: C53.2, R126.2
unnamed: C54.1, R30.1, R34.2, SW7.A
unnamed: C55.1, R31.2, R35.1, SW7.B
unnamed: C60.1, C61.1, C63.1, J4.2, R38.2
unnamed: C60.2, R39.1
unnamed: C63.2, C66.1, C67.1, J4.3, R37.1
unnamed: C66.2, R42.1
unnamed: D1.1 (DOUT), D2.3 (DIN)
unnamed: D2.1 (DOUT), D3.3 (DIN)
unnamed: D3.1 (DOUT), D4.3 (DIN)
unnamed: D4.1 (DOUT), D5.3 (DIN)
unnamed: D5.1 (DOUT), D6.3 (DIN)
unnamed: D6.1 (DOUT), D7.3 (DIN)
unnamed: D7.1 (DOUT), D8.3 (DIN)
unnamed: C26.2, C30.2, D10.1 (A1), R13.2, R14.2, U2.10 (IN2)
unnamed: C24.1, C26.1, D11.2 (A2), R10.2, R11.1, U2.7 (IN1)
unnamed: C32.1, C64.1, D12.2 (A2), R22.1, R39.2, U7.7 (IN1)
unnamed: D13.2 (A), R4.2
unnamed: C34.2, C64.2, D14.1 (A1), R27.2, R42.2, U7.10 (IN2)
unnamed: D18.1 (DOUT), D19.3 (DIN)
unnamed: D19.1 (DOUT), D20.3 (DIN)
unnamed: D20.1 (DOUT), D21.3 (DIN)
unnamed: D21.1 (DOUT), D22.3 (DIN)
unnamed: D22.1 (DOUT), D23.3 (DIN)
unnamed: D23.1 (DOUT), D24.3 (DIN)
unnamed: D24.1 (DOUT), D25.3 (DIN)
unnamed: D30.2 (A), R33.2
unnamed: Q1.3 (D), U9.7 (PD_N)
unnamed: Q5.3 (D), U3.7 (PD_N)
unnamed: C37.1, J3.R, SW3.3 (S1), SW3.14 (S2)
unnamed: C100.2, D66.3 (K), R87.1, SW3.15 (D2)
unnamed: C104.2, R80.1, SW3.10 (D3)
unnamed: C36.1, D65.3 (K), J3.T, SW3.6 (S4), SW3.11 (S3)
unnamed: R121.1, SW3.7 (D4)
unnamed: R24.2, R25.1, SW4.2 (D1), SW4.14 (S2)
unnamed: R24.1, SW4.3 (S1), SW6.2 (D1), SW6.15 (D2)
unnamed: R25.2, R26.1, SW4.15 (D2)
unnamed: R20.2, R21.1, SW4.6 (S4), SW4.10 (D3)
unnamed: R19.2, R20.1, SW4.11 (S3)
unnamed: R21.2, R128.1, SW4.7 (D4), SW5.6 (S4), U5.1
unnamed: R16.1, SW5.2 (D1), SW5.15 (D2)
unnamed: R127.2, SW5.3 (S1), U5.7
unnamed: R28.1, SW5.7 (D4), SW5.10 (D3)
unnamed: SW6.3 (S1), U6.1, U6.2 (-)
unnamed: SW6.14 (S2), U14.13 (OUT)
unnamed: SW6.11 (S3), U14.8 (OUT)
unnamed: SW6.6 (S4), U6.6 (-), U6.7
unnamed: C76.1, J4.R, SW9.3 (S1), SW9.14 (S2)
unnamed: C106.2, D68.3 (K), R137.1, SW9.15 (D2)
unnamed: C115.2, R134.1, SW9.10 (D3)
unnamed: C75.1, D67.3 (K), J4.T, SW9.6 (S4), SW9.11 (S3)
unnamed: R41.1, SW9.7 (D4)
unnamed: R55.2, R56.1, SW10.2 (D1), SW10.14 (S2)
unnamed: R55.1, SW6.7 (D4), SW6.10 (D3), SW10.3 (S1)
unnamed: R56.2, R57.1, SW10.15 (D2)
unnamed: R51.2, R52.1, SW10.6 (S4), SW10.10 (D3)
unnamed: R50.2, R51.1, SW10.11 (S3)
unnamed: R52.2, R129.1, SW10.7 (D4), SW11.6 (S4), U24.1
unnamed: R47.1, SW11.2 (D1), SW11.15 (D2)
unnamed: R130.2, SW11.3 (S1), U24.7
unnamed: R59.1, SW11.7 (D4), SW11.10 (D3)
unnamed: C15.1, U1.6 (RA_CH1), U2.6 (Rg1)
unnamed: R5.1, U1.8 (RG2_CH1), U1.9 (RB_CH1), U2.15 (Rg2)
unnamed: C15.2, R5.2, U1.7 (RG1_CH1)
unnamed: C14.1, U1.22 (RA_CH2), U7.6 (Rg1)
unnamed: R36.1, U1.1 (RB_CH2), U1.24 (RG2_CH2), U7.15 (Rg2)
unnamed: C14.2, R36.2, U1.23 (RG1_CH2)
unnamed: R16.2, R17.1, R23.2, U3.8 (VIN+)
unnamed: R23.1, R28.2, R29.2, U3.1 (VIN-)
unnamed: R29.1, R124.1, U3.4 (VOUT+)
unnamed: R17.2, R123.1, U3.5 (VOUT-)
unnamed: R19.1, R26.2, U5.2 (-)
unnamed: R127.1, R128.2, U5.5 (+)
unnamed: R121.2, U6.3 (+)
unnamed: R41.2, U6.5 (+)
unnamed: R45.1, U8.1 (~INT)
unnamed: R43.1, U8.24 (~RESET)
unnamed: R47.2, R48.1, R54.2, U9.8 (VIN+)
unnamed: R54.1, R59.2, R60.2, U9.1 (VIN-)
unnamed: R60.1, R126.1, U9.4 (VOUT+)
unnamed: R48.2, R125.1, U9.5 (VOUT-)
unnamed: R12.2, U14.3 (COM)
unnamed: C100.1, U14.2 (IN+)
unnamed: C104.1, U14.4 (IN-)
unnamed: R15.2, U14.6 (COM)
unnamed: C106.1, U14.7 (IN+)
unnamed: C115.1, U14.5 (IN-)
unnamed: R50.1, R57.2, U24.2 (-)
unnamed: R129.2, R130.1, U24.5 (+)

Notes on the sheet:
ref 6.
design note: The OPA1637's output current is limited to +/-31mA, so the clamping diodes at the TAC5212 inputs will never see more than this. This means the series resistor value doesn't matter and only servers to isolate the circuit, not limit the current through the schottky diodes.
1100 = -12dB 0100 = -6dB 0000 = 0dB 0010 = +6dB 0011 = +12dB

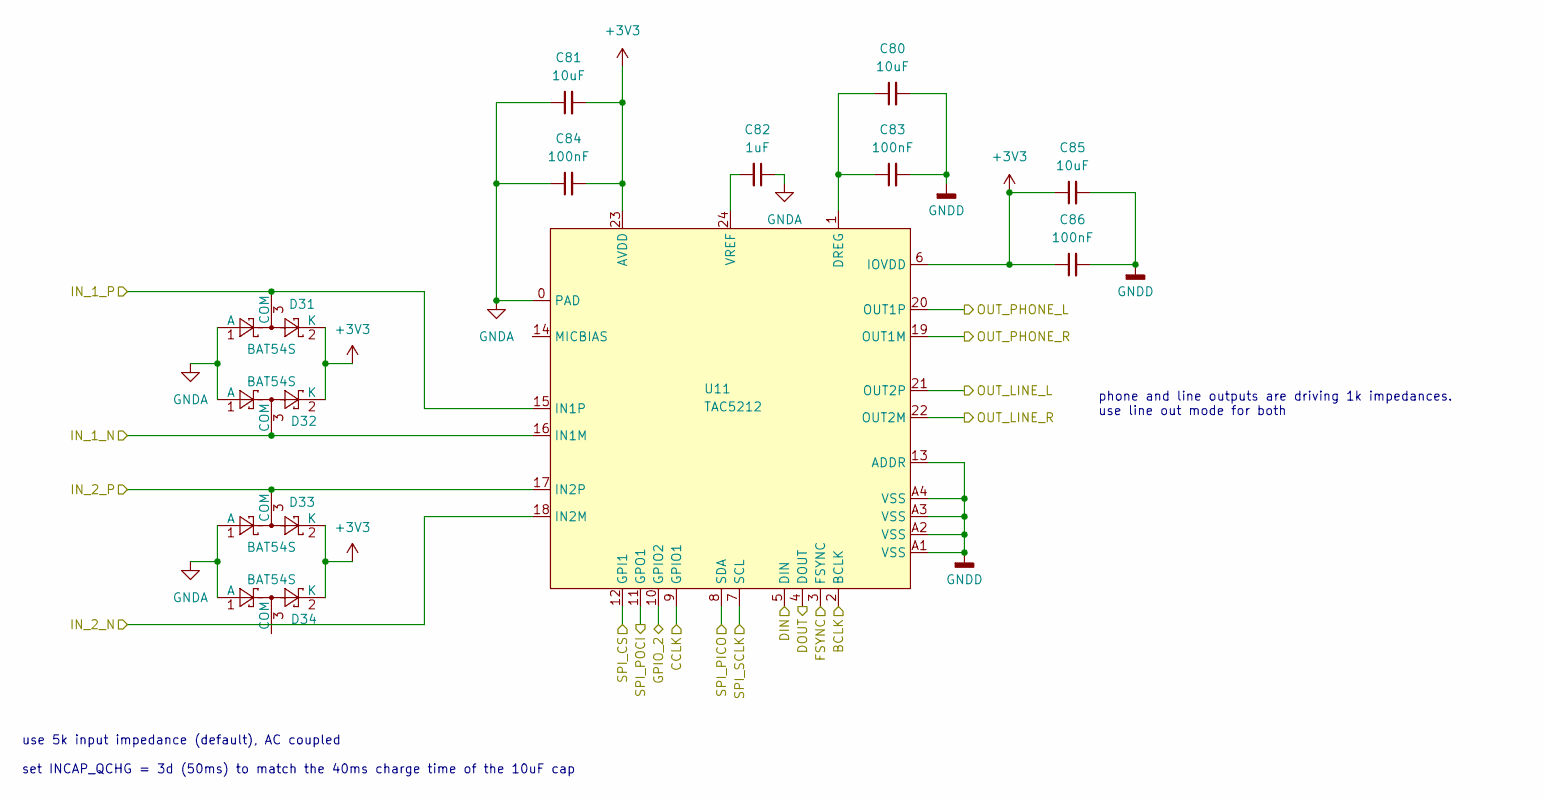
[picture p49: schematic codec.kicad_sch, Audio codec]

Parts:
C80, C81, C85: 10uF; C_0603_1608Metric_Pad1.08x0.95mm_HandSolder
C82: 1uF; C_0603_1608Metric_Pad1.08x0.95mm_HandSolder
C83, C84, C86: 100nF; C_0603_1608Metric_Pad1.08x0.95mm_HandSolder
D31, D32, D33, D34: BAT54S; SOT-23
U11: TAC5212

Connections:
+3V3: C81.2, C84.2, C85.1, C86.1, D31.2 (K), D32.2 (K), D33.2 (K), D34.2 (K), U11.6 (IOVDD), U11.23 (AVDD); also elsewhere on the board
/codec/GPIO_2: U11.10 (GPIO2)
/codec/IN_1_N: D32.3 (COM), U11.16 (IN1M); also elsewhere on the board
/codec/IN_1_P: D31.3 (COM), U11.15 (IN1P); also elsewhere on the board
/codec/IN_2_N: U11.18 (IN2M); also elsewhere on the board
/codec/IN_2_P: D33.3 (COM), U11.17 (IN2P); also elsewhere on the board
/codec/OUT_LINE_L: U11.21 (OUT2P); also elsewhere on the board
/codec/OUT_LINE_R: U11.22 (OUT2M); also elsewhere on the board
/codec/OUT_PHONE_L: U11.20 (OUT1P); also elsewhere on the board
/codec/OUT_PHONE_R: U11.19 (OUT1M); also elsewhere on the board
/usb bridge/GP0_1D: U11.11 (GPO1); also elsewhere on the board
/usb bridge/GP0_1I: U11.8 (SDA); also elsewhere on the board
/usb bridge/GP0_1J: U11.7 (SCL); also elsewhere on the board
/usb bridge/GP0_8C_2: U11.12 (GPI1); also elsewhere on the board
/usb bridge/GP1_1A: U11.2 (BCLK); also elsewhere on the board
/usb bridge/GP1_1B: U11.3 (FSYNC); also elsewhere on the board
/usb bridge/GP1_1C: U11.9 (GPIO1); also elsewhere on the board
/usb bridge/GP1_1D: U11.5 (DIN); also elsewhere on the board
/usb bridge/GP1_1F: U11.4 (DOUT); also elsewhere on the board
Earth: C80.2, C81.1, C82.1, C83.2, C84.1, C85.2, C86.2, D31.1 (A), D32.1 (A), D33.1 (A), D34.1 (A), U11.0 (PAD), U11.13 (ADDR), U11.A1 (VSS), U11.A2 (VSS), U11.A3 (VSS), U11.A4 (VSS); also elsewhere on the board
unnamed: C80.1, C83.1, U11.1 (DREG)
unnamed: C82.2, U11.24 (VREF)

Notes on the sheet:
phone and line outputs are driving 1k impedances. use line out mode for both
use 5k input impedance (default), AC coupled set INCAP_QCHG = 3d (50ms) to match the 40ms charge time of the 10uF cap

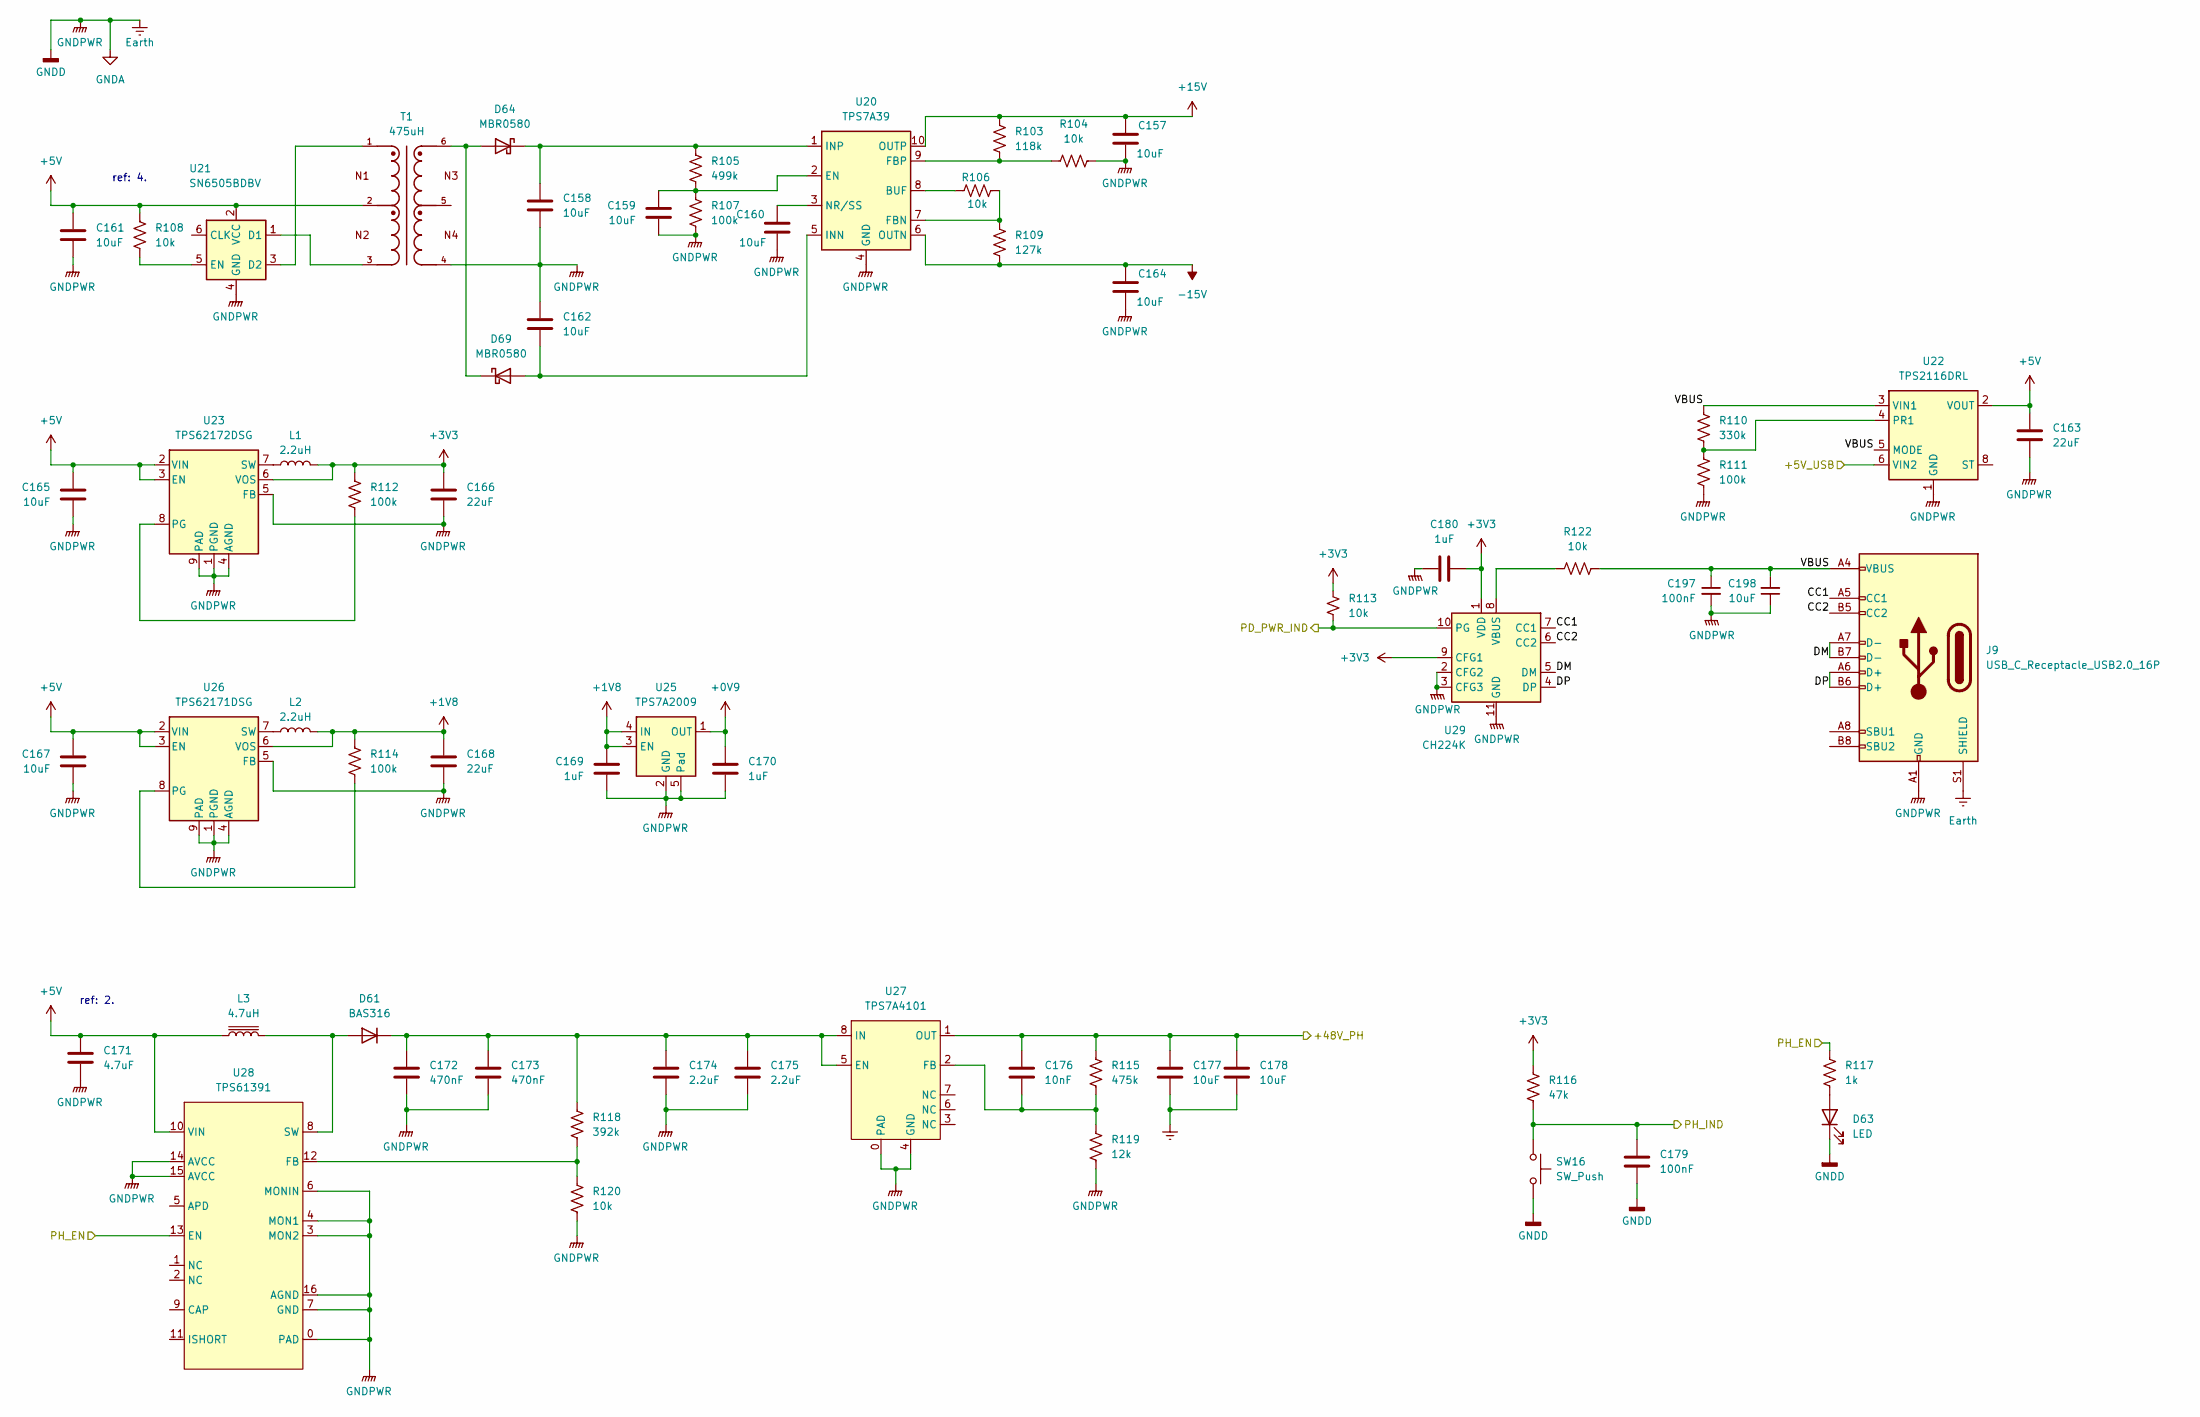
[picture p50: schematic power.kicad_sch, Power supply]

Parts:
C157, C158, C159, C160, C161, C162, C164, C165, C167, C177, C178, C198: 10uF; C_0805_2012Metric_Pad1.18x1.45mm_HandSolder
C163, C166, C168: 22uF; C_0805_2012Metric_Pad1.18x1.45mm_HandSolder
C169, C170, C180: 1uF; C_0805_2012Metric_Pad1.18x1.45mm_HandSolder
C171: 4.7uF; C_0805_2012Metric_Pad1.18x1.45mm_HandSolder
C172, C173: 470nF; C_0805_2012Metric_Pad1.18x1.45mm_HandSolder
C174, C175: 2.2uF; C_0805_2012Metric_Pad1.18x1.45mm_HandSolder
C176: 10nF; C_0805_2012Metric_Pad1.18x1.45mm_HandSolder
C179: 100nF; C_0603_1608Metric_Pad1.08x0.95mm_HandSolder
C197: 100nF; C_0805_2012Metric_Pad1.18x1.45mm_HandSolder
D61: BAS316; D_SOD-323
D63: LED; LED_0603_1608Metric_Pad1.05x0.95mm_HandSolder
D64, D69: MBR0580; D_SOD-123
J9: USB_C_Receptacle_USB2.0_16P; USB_C_Receptacle_HRO_TYPE-C-31-M-12
L1, L2: 2.2uH; L_Wuerth_PMCI-201610
L3: 4.7uH; L_Wuerth_PMCI-201610
R103: 118k; R_0805_2012Metric_Pad1.20x1.40mm_HandSolder
R104, R106, R108, R120, R122: 10k; R_0805_2012Metric_Pad1.20x1.40mm_HandSolder
R105: 499k; R_0805_2012Metric_Pad1.20x1.40mm_HandSolder
R107, R111, R112, R114: 100k; R_0805_2012Metric_Pad1.20x1.40mm_HandSolder
R109: 127k; R_0805_2012Metric_Pad1.20x1.40mm_HandSolder
R110: 330k; R_0805_2012Metric_Pad1.20x1.40mm_HandSolder
R113: 10k; R_0603_1608Metric_Pad0.98x0.95mm_HandSolder
R115: 475k; R_0805_2012Metric_Pad1.20x1.40mm_HandSolder
R116: 47k; R_0603_1608Metric_Pad0.98x0.95mm_HandSolder
R117: 1k; R_0603_1608Metric_Pad0.98x0.95mm_HandSolder
R118: 392k; R_0805_2012Metric_Pad1.20x1.40mm_HandSolder
R119: 12k; R_0805_2012Metric_Pad1.20x1.40mm_HandSolder
SW16: SW_Push; SW_Push_1P1T_XKB_TS-1187A
T1: 475uH; Wurth Elektronik 760390015
U20: TPS7A39; Texas_S-PVSON-N10_ThermalVias
U21: SN6505BDBV; SOT-23-6
U22: TPS2116DRL; SOT-583-8
U23: TPS62172DSG; WSON-8-1EP_2x2mm_P0.5mm_EP0.9x1.6mm_ThermalVias
U25: TPS7A2009; Texas_X2SON-4_1x1mm_P0.65mm
U26: TPS62171DSG; WSON-8-1EP_2x2mm_P0.5mm_EP0.9x1.6mm_ThermalVias
U27: TPS7A4101; Texas_DGN0008B_VSSOP-8-1EP_3x3mm_P0.65mm_EP2x3mm_Mask1.88x1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
U28: TPS61391; WQFN-16-1EP_3x3mm_P0.5mm_EP1.6x1.6mm
U29: CH224K; SSOP-10-1EP_3.9x4.9mm_P1mm_EP2.1x3.3mm

Connections:
+0V9: C170.1, U25.1 (OUT); also elsewhere on the board
+1V8: C168.1, C169.1, L2.2, R114.1, U25.3 (EN), U25.4 (IN), U26.6 (VOS); also elsewhere on the board
+3V3: C166.1, C180.1, L1.2, R112.1, R113.1, R116.1, U23.6 (VOS), U29.1 (VDD), U29.9 (CFG1); also elsewhere on the board
+5V: C161.1, C163.1, C165.1, C167.1, C171.1, L3.1, R108.2, T1.2, U21.2 (VCC), U22.2 (VOUT), U22.7 (VOUT), U23.2 (VIN), U23.3 (EN), U26.2 (VIN), U26.3 (EN), U28.10 (VIN); also elsewhere on the board
+15V: C157.1, R103.1, U20.10 (OUTP); also elsewhere on the board
-15V: C164.1, R109.2, U20.6 (OUTN); also elsewhere on the board
/input/+48V_PH: C176.1, C177.1, C178.1, R115.1, U27.1 (OUT); also elsewhere on the board
/power supply/CC1: J9.A5 (CC1), U29.7 (CC1)
/power supply/CC2: J9.B5 (CC2), U29.6 (CC2)
/power supply/DM: J9.A7 (D-), J9.B7 (D-), U29.5 (DM)
/power supply/DP: J9.A6 (D+), J9.B6 (D+), U29.4 (DP)
/power supply/VBUS: C197.1, C198.2, J9.A4 (VBUS), J9.A9 (VBUS), J9.B4 (VBUS), J9.B9 (VBUS), R110.1, R122.2, U22.3 (VIN1), U22.5 (MODE)
/usb bridge/GP0_8C_3: R117.1, U28.13 (EN); also elsewhere on the board
/usb bridge/GP0_8D_1: R113.2, U29.10 (PG); also elsewhere on the board
/usb bridge/GP0_8D_3: C179.1, R116.2, SW16.1; also elsewhere on the board
/usb bridge/VBUS: U22.6 (VIN2); also elsewhere on the board
Earth: C157.2, C158.2, C159.2, C160.2, C161.2, C162.1, C163.2, C164.2, C165.2, C166.2, C167.2, C168.2, C169.2, C170.2, C171.2, C172.2, C173.2, C174.2, C175.2, C177.2, C178.2, C179.2, C180.2, C197.2, C198.1, D63.1 (K), J9.A1 (GND), J9.A12 (GND), J9.B1 (GND), J9.B12 (GND), J9.S1 (SHIELD), R104.2, R107.2, R111.2, R119.2, R120.2, SW16.2, T1.4, U20.4 (GND), U20.11 (GND), U21.4 (GND), U22.1 (GND), U23.1 (PGND), U23.4 (AGND), U23.5 (FB), U23.9 (PAD), U25.2 (GND), U25.5 (Pad), U26.1 (PGND), U26.4 (AGND), U26.5 (FB), U26.9 (PAD), U27.0 (PAD), U27.4 (GND), U28.0 (PAD), U28.3 (MON2), U28.4 (MON1), U28.6 (MONIN), U28.7 (GND), U28.14 (AVCC), U28.15 (AVCC), U28.16 (AGND), U29.2 (CFG2), U29.3 (CFG3), U29.11 (GND); also elsewhere on the board
unnamed: D61.2 (A), L3.2, U28.8 (SW)
unnamed: C172.1, C173.1, C174.1, C175.1, D61.1 (K), R118.1, U27.5 (EN), U27.8 (IN)
unnamed: D63.2 (A), R117.2
unnamed: D64.2 (A), D69.1 (K), T1.6
unnamed: C158.1, D64.1 (K), R105.1, U20.1 (INP)
unnamed: C162.2, D69.2 (A), U20.5 (INN)
unnamed: R106.1, U20.8 (BUF)
unnamed: C159.1, R105.2, R107.1, U20.2 (EN)
unnamed: R106.2, R109.1, U20.7 (FBN)
unnamed: R103.2, R104.1, U20.9 (FBP)
unnamed: C160.1, U20.3 (NR/SS)
unnamed: T1.3, U21.1 (D1)
unnamed: T1.1, U21.3 (D2)
unnamed: R108.1, U21.5 (EN)
unnamed: R110.2, R111.1, U22.4 (PR1)
unnamed: R112.2, U23.8 (PG)
unnamed: L1.1, U23.7 (SW)
unnamed: R114.2, U26.8 (PG)
unnamed: L2.1, U26.7 (SW)
unnamed: C176.2, R115.2, R119.1, U27.2 (FB)
unnamed: R118.2, R120.1, U28.12 (FB)
unnamed: R122.1, U29.8 (VBUS)

Notes on the sheet:
ref: 4.
ref: 2.
