oliverpaddock/OpenMic/hardware/pcb/main-board/openmic.kicad_pcb

## KiCad design hardware/pcb/main-board/openmic.kicad_pcb (continued)

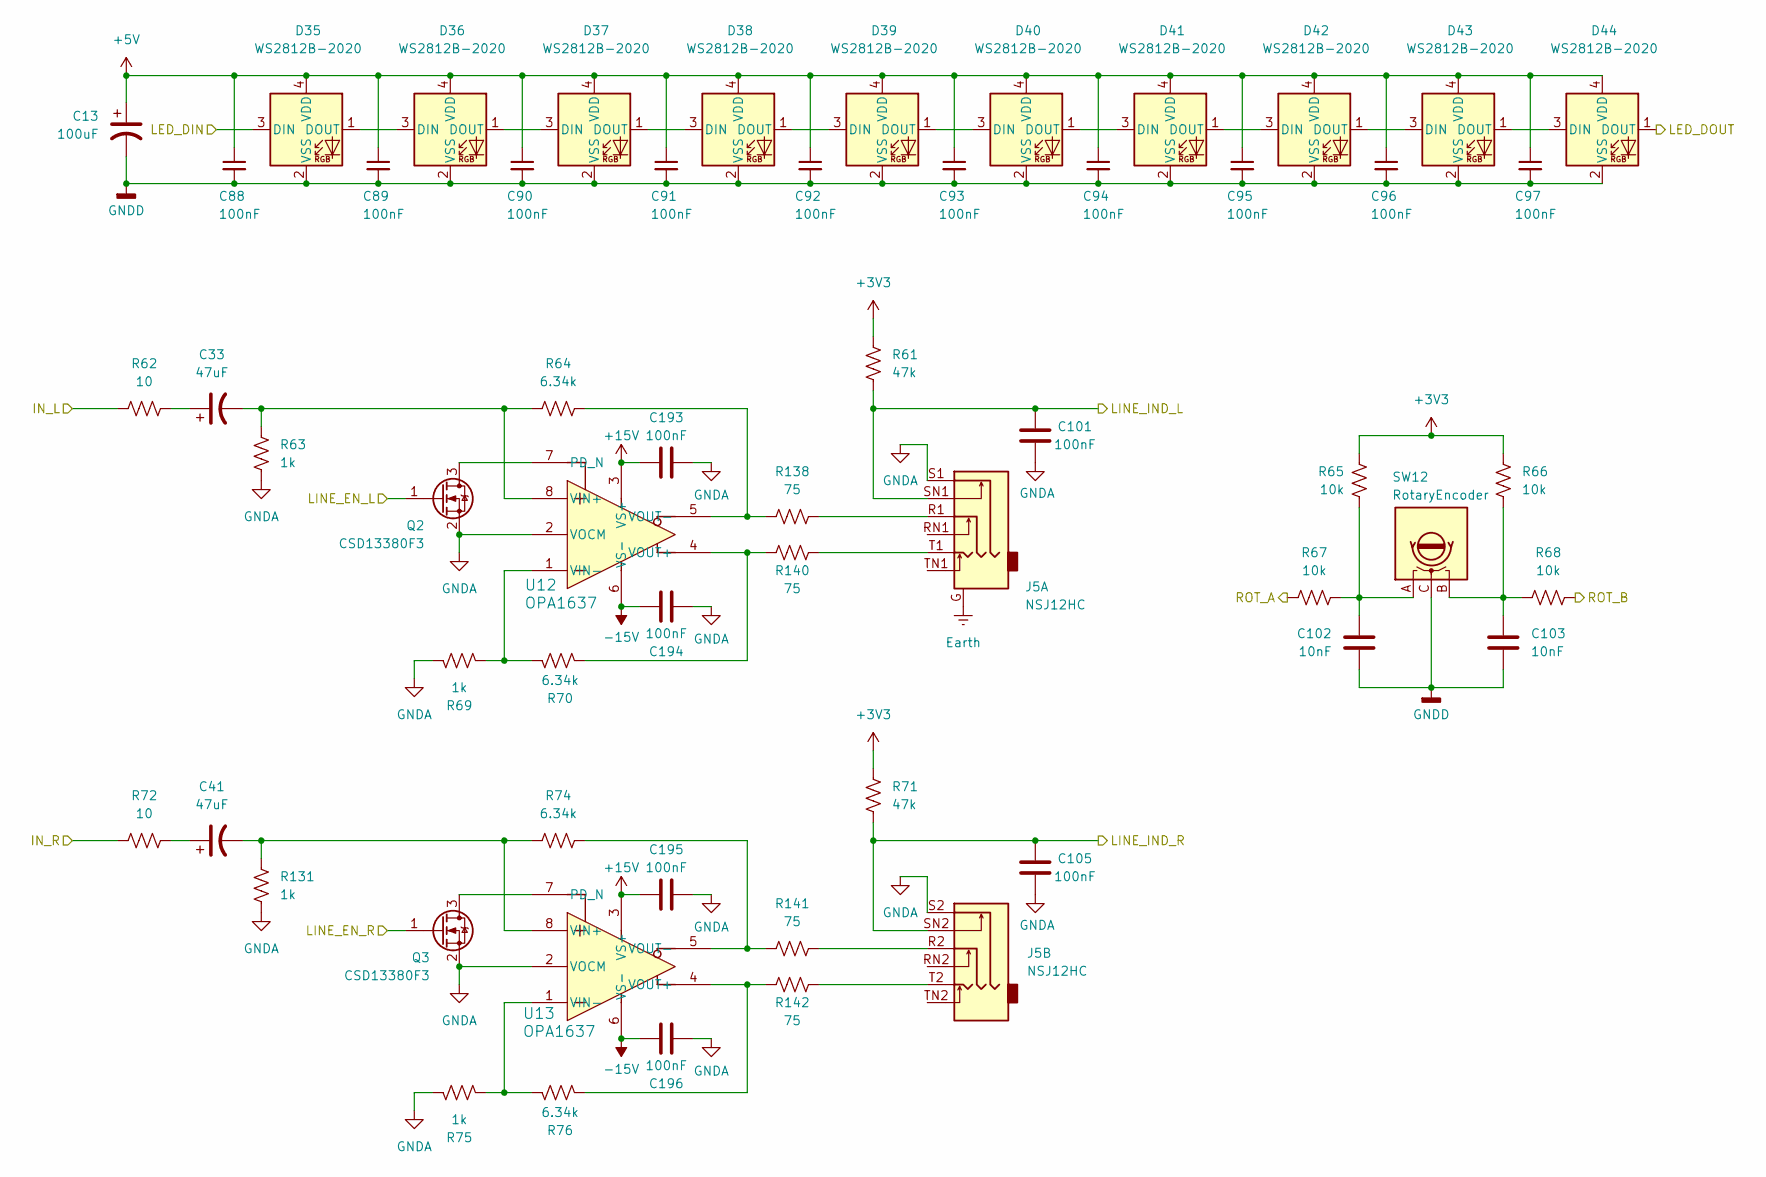
[picture p51: schematic line.kicad_sch, Line out]

Parts:
C13: 100uF; CP_Elec_6.3x5.4
C33, C41: 47uF; CP_Elec_6.3x5.4
C88, C89, C90, C91, C92, C93, C94, C95, C96, C97, C101, C105, C193, C194, C195, C196: 100nF; C_0603_1608Metric_Pad1.08x0.95mm_HandSolder
C102, C103: 10nF; C_0603_1608Metric_Pad1.08x0.95mm_HandSolder
D35, D36, D37, D38, D39, D40, D41, D42, D43, D44: WS2812B-2020; LED_WS2812B-2020_PLCC4_2.0x2.0mm
J5: NSJ12HC; Jack_6.35mm_Neutrik_NSJ12HC_Horizontal
Q2, Q3: CSD13380F3; Texas_PicoStar_DFN-3_0.69x0.60mm
R61, R71: 47k; R_0603_1608Metric_Pad0.98x0.95mm_HandSolder
R62, R72: 10; R_0603_1608Metric_Pad0.98x0.95mm_HandSolder
R63, R69, R75, R131: 1k; R_0603_1608Metric_Pad0.98x0.95mm_HandSolder
R64, R70, R74, R76: 6.34k; R_0603_1608Metric_Pad0.98x0.95mm_HandSolder
R65, R66, R67, R68: 10k; R_0603_1608Metric_Pad0.98x0.95mm_HandSolder
R138, R140, R141, R142: 75; R_0603_1608Metric_Pad0.98x0.95mm_HandSolder
SW12: RotaryEncoder; PEC11L
U12, U13: OPA1637; VSSOP-8_3x3mm_P0.65mm

Connections:
+3V3: R61.1, R65.2, R66.1, R71.1; also elsewhere on the board
+5V: C13.1, C88.1, C89.1, C90.1, C91.1, C92.1, C93.1, C94.1, C95.1, C96.1, C97.1, D35.4 (VDD), D36.4 (VDD), D37.4 (VDD), D38.4 (VDD), D39.4 (VDD), D40.4 (VDD), D41.4 (VDD), D42.4 (VDD), D43.4 (VDD), D44.4 (VDD); also elsewhere on the board
+15V: C193.1, C195.1, U12.3 (VS+), U13.3 (VS+); also elsewhere on the board
-15V: C194.1, C196.1, U12.6 (VS-), U13.6 (VS-); also elsewhere on the board
/codec/OUT_LINE_L: R62.1; also elsewhere on the board
/codec/OUT_LINE_R: R72.1; also elsewhere on the board
/line driver/LED_DIN: D35.3 (DIN); also elsewhere on the board
/line driver/LED_DOUT: D44.1 (DOUT)
/usb bridge/GP0_8C_5: Q2.1 (G); also elsewhere on the board
/usb bridge/GP0_8C_6: Q3.1 (G); also elsewhere on the board
/usb bridge/GP0_8D_5: C101.1, J5.SN1, R61.2; also elsewhere on the board
/usb bridge/GP0_8D_6: C105.1, J5.SN2, R71.2; also elsewhere on the board
/usb bridge/GP1_1N: R67.1; also elsewhere on the board
/usb bridge/GP1_1O: R68.2; also elsewhere on the board
Earth: C13.2, C88.2, C89.2, C90.2, C91.2, C92.2, C93.2, C94.2, C95.2, C96.2, C97.2, C101.2, C102.2, C103.2, C105.2, C193.2, C194.2, C195.2, C196.2, D35.2 (VSS), D36.2 (VSS), D37.2 (VSS), D38.2 (VSS), D39.2 (VSS), D40.2 (VSS), D41.2 (VSS), D42.2 (VSS), D43.2 (VSS), D44.2 (VSS), J5.G, J5.S1, J5.S2, Q2.2 (S), Q3.2 (S), R63.1, R69.1, R75.1, R131.1, SW12.C, U12.2 (VOCM), U13.2 (VOCM); also elsewhere on the board
unnamed: C33.1, R62.2
unnamed: C41.1, R72.2
unnamed: C102.1, R65.1, R67.2, SW12.A
unnamed: C103.1, R66.2, R68.1, SW12.B
unnamed: D35.1 (DOUT), D36.3 (DIN)
unnamed: D36.1 (DOUT), D37.3 (DIN)
unnamed: D37.1 (DOUT), D38.3 (DIN)
unnamed: D38.1 (DOUT), D39.3 (DIN)
unnamed: D39.1 (DOUT), D40.3 (DIN)
unnamed: D40.1 (DOUT), D41.3 (DIN)
unnamed: D41.1 (DOUT), D42.3 (DIN)
unnamed: D42.1 (DOUT), D43.3 (DIN)
unnamed: D43.1 (DOUT), D44.3 (DIN)
unnamed: J5.R1, R138.2
unnamed: J5.R2, R141.2
unnamed: J5.T1, R140.1
unnamed: J5.T2, R142.1
unnamed: Q2.3 (D), U12.7 (PD_N)
unnamed: Q3.3 (D), U13.7 (PD_N)
unnamed: C33.2, R63.2, R64.1, U12.8 (VIN+)
unnamed: R69.2, R70.2, U12.1 (VIN-)
unnamed: R70.1, R140.2, U12.4 (VOUT+)
unnamed: R64.2, R138.1, U12.5 (VOUT-)
unnamed: C41.2, R74.1, R131.2, U13.8 (VIN+)
unnamed: R75.2, R76.2, U13.1 (VIN-)
unnamed: R76.1, R142.2, U13.4 (VOUT+)
unnamed: R74.2, R141.1, U13.5 (VOUT-)

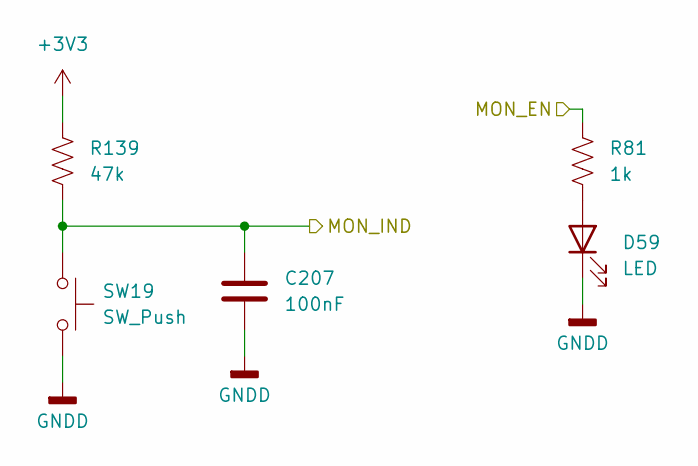
[picture p52: schematic monitor.kicad_sch, Direct monitor switch]

Parts:
C207: 100nF; C_0603_1608Metric_Pad1.08x0.95mm_HandSolder
D59: LED; LED_0603_1608Metric_Pad1.05x0.95mm_HandSolder
R81: 1k; R_0603_1608Metric_Pad0.98x0.95mm_HandSolder
R139: 47k; R_0603_1608Metric_Pad0.98x0.95mm_HandSolder
SW19: SW_Push; SW_Push_1P1T_XKB_TS-1187A

Connections:
+3V3: R139.1; also elsewhere on the board
/usb bridge/GP0_8C_7: R81.1; also elsewhere on the board
/usb bridge/GP0_8D_7: C207.1, R139.2, SW19.1; also elsewhere on the board
Earth: C207.2, D59.1 (K), SW19.2; also elsewhere on the board
unnamed: D59.2 (A), R81.2

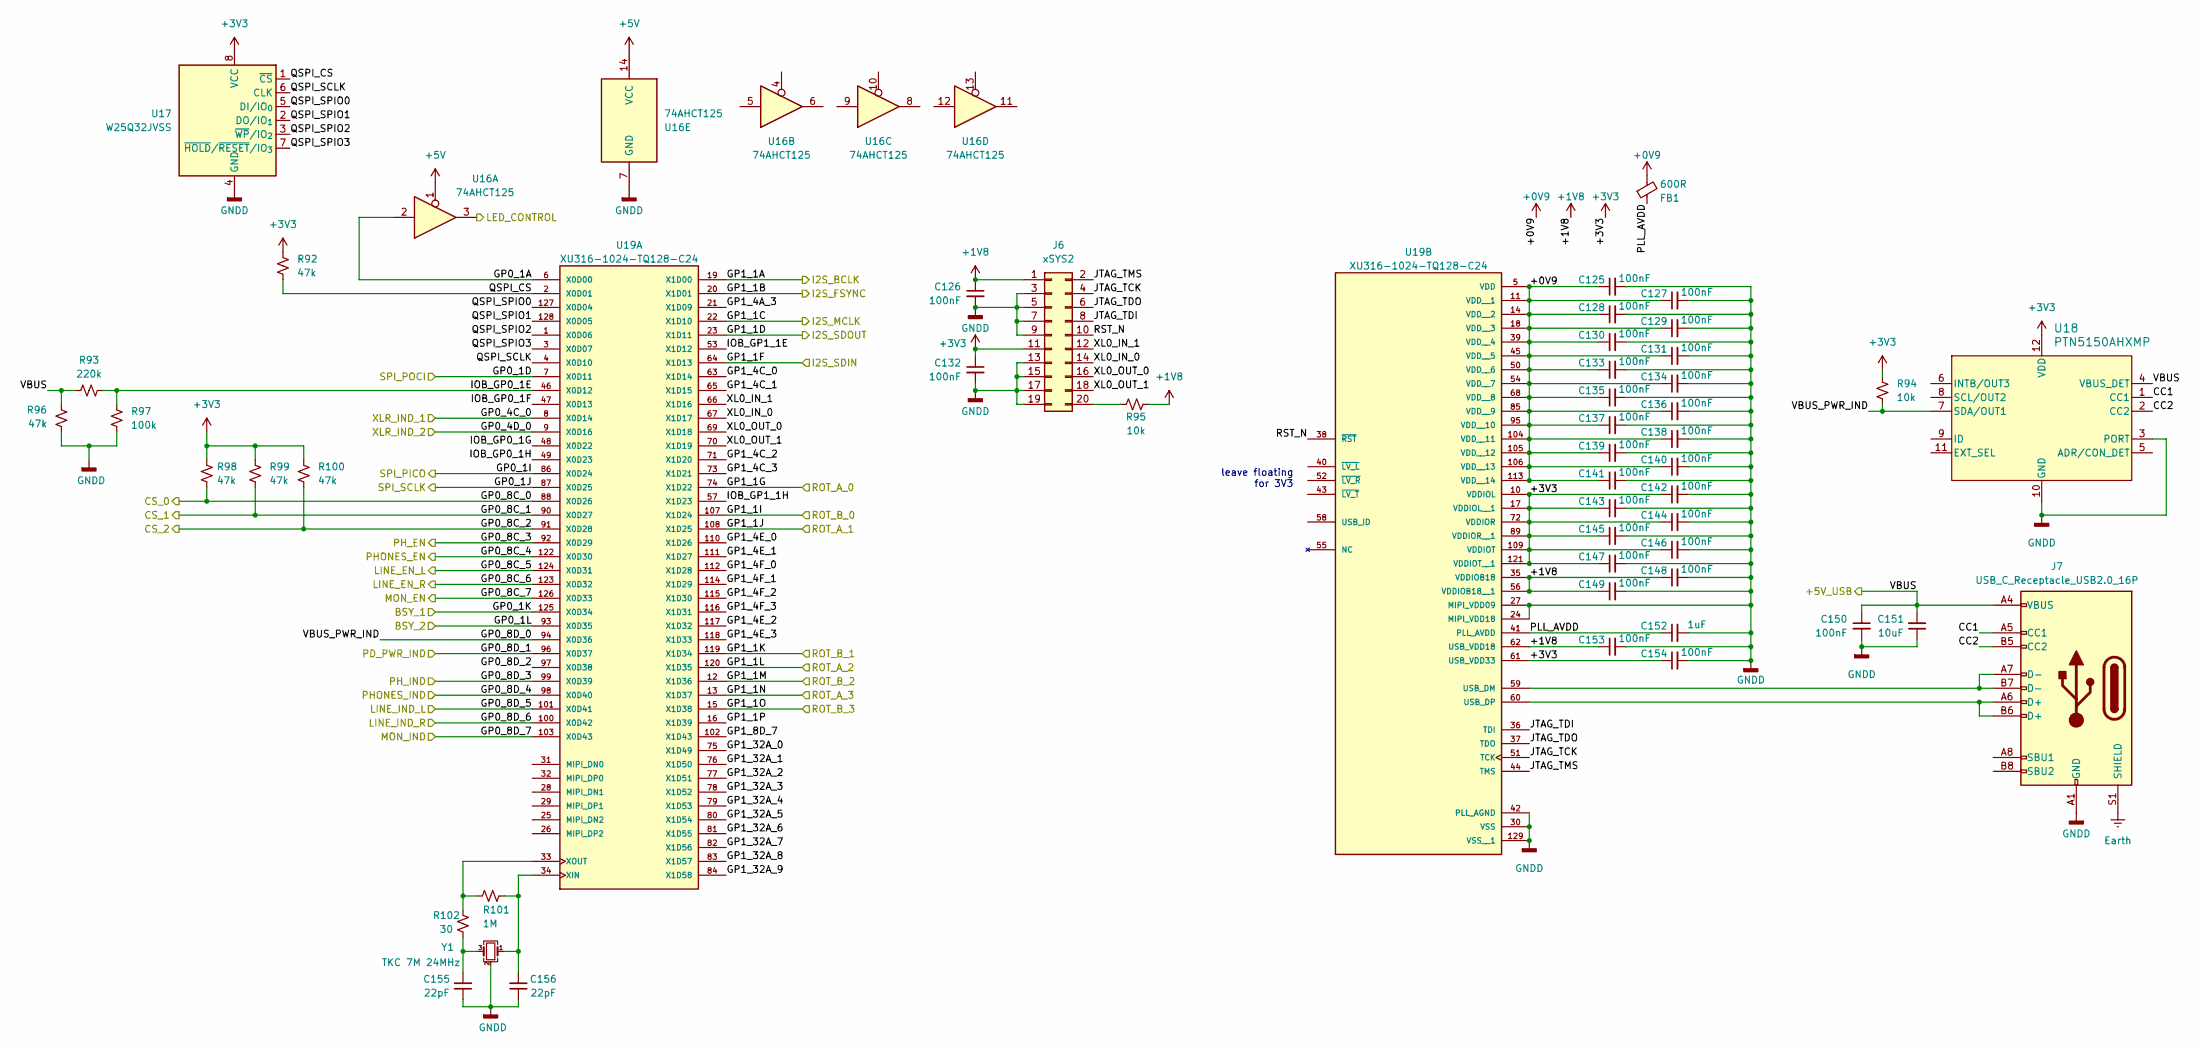
[picture p53: schematic usb.kicad_sch, MCU]

Parts:
C125, C127, C128, C129, C130, C131, C133, C134, C135, C136, C137, C138, C139, C140, C141, C142, C143, C144, C145, C146, C147, C148, C149, C153, C154: 100nF; C_0402_1005Metric_Pad0.74x0.62mm_HandSolder
C126, C132: 100nF; C_0603_1608Metric_Pad1.08x0.95mm_HandSolder
C150: 100nF; C_0805_2012Metric_Pad1.18x1.45mm_HandSolder
C151: 10uF; C_0805_2012Metric_Pad1.18x1.45mm_HandSolder
C152: 1uF; C_0402_1005Metric_Pad0.74x0.62mm_HandSolder
C155, C156: 22pF; C_0603_1608Metric_Pad1.08x0.95mm_HandSolder
FB1: 600R; L_0402_1005Metric_Pad0.77x0.64mm_HandSolder
J6: xSYS2; PinHeader_2x10_P1.27mm_Vertical_SMD
J7: USB_C_Receptacle_USB2.0_16P; USB_C_Receptacle_HRO_TYPE-C-31-M-12
R92, R96, R98, R99, R100: 47k; R_0603_1608Metric_Pad0.98x0.95mm_HandSolder
R93: 220k; R_0603_1608Metric_Pad0.98x0.95mm_HandSolder
R94, R95: 10k; R_0603_1608Metric_Pad0.98x0.95mm_HandSolder
R97: 100k; R_0603_1608Metric_Pad0.98x0.95mm_HandSolder
R101: 1M; R_0603_1608Metric_Pad0.98x0.95mm_HandSolder
R102: 30; R_0603_1608Metric_Pad0.98x0.95mm_HandSolder
U16: 74AHCT125; SOIC-14_3.9x8.7mm_P1.27mm
U17: W25Q32JVSS; SOIC-8_5.3x5.3mm_P1.27mm
U18: PTN5150AHXMP; Texas_X2QFN-12_1.6x1.6mm_P0.4mm
U19: XU316-1024-TQ128-C24; XU316-TQ128; PARTREV 2025/1/13
Y1: TKC 7M 24MHz; Crystal_SMD_TXC_7M-4Pin_3.2x2.5mm_HandSoldering

Connections:
+0V9: C125.1, C127.1, C128.1, C129.1, C130.1, C131.1, C133.1, C134.1, C135.1, C136.1, C137.1, C138.1, C139.1, C140.1, C141.1, FB1.2, U19.5 (VDD), U19.11 (VDD__1), U19.14 (VDD__2), U19.18 (VDD__3), U19.39 (VDD__4), U19.45 (VDD__5), U19.50 (VDD__6), U19.54 (VDD__7), U19.68 (VDD__8), U19.85 (VDD__9), U19.95 (VDD__10), U19.104 (VDD__11), U19.105 (VDD__12), U19.106 (VDD__13), U19.113 (VDD__14); also elsewhere on the board
+1V8: C126.1, C148.1, C149.1, C153.1, J6.1, R95.1, U19.35 (VDDIOB18), U19.56 (VDDIOB18__1), U19.62 (USB_VDD18); also elsewhere on the board
+3V3: C132.1, C142.1, C143.1, C144.1, C145.1, C146.1, C147.1, C154.1, J6.11, R92.1, R94.1, R98.1, R99.1, R100.1, U17.8 (VCC), U18.12 (VDD), U19.10 (VDDIOL), U19.17 (VDDIOL__1), U19.61 (USB_VDD33), U19.72 (VDDIOR), U19.89 (VDDIOR__1), U19.109 (VDDIOT), U19.121 (VDDIOT__1); also elsewhere on the board
+5V: U16.1, U16.14 (VCC); also elsewhere on the board
/input/LED_1_DIN: U16.3; also elsewhere on the board
/usb bridge/CC1: J7.A5 (CC1), U18.1 (CC1)
/usb bridge/CC2: J7.B5 (CC2), U18.2 (CC2)
/usb bridge/GP0_1A: U16.2, U19.6 (X0D00)
/usb bridge/GP0_1D: U19.7 (X0D11); also elsewhere on the board
/usb bridge/GP0_1I: U19.86 (X0D24); also elsewhere on the board
/usb bridge/GP0_1J: U19.87 (X0D25); also elsewhere on the board
/usb bridge/GP0_1K: U19.125 (X0D34); also elsewhere on the board
/usb bridge/GP0_1L: U19.93 (X0D35); also elsewhere on the board
/usb bridge/GP0_4C_0: U19.8 (X0D14); also elsewhere on the board
/usb bridge/GP0_4D_0: U19.9 (X0D16); also elsewhere on the board
/usb bridge/GP0_8C_0: R98.2, U19.88 (X0D26); also elsewhere on the board
/usb bridge/GP0_8C_1: R99.2, U19.90 (X0D27); also elsewhere on the board
/usb bridge/GP0_8C_2: R100.2, U19.91 (X0D28); also elsewhere on the board
/usb bridge/GP0_8C_3: U19.92 (X0D29); also elsewhere on the board
/usb bridge/GP0_8C_4: U19.122 (X0D30); also elsewhere on the board
/usb bridge/GP0_8C_5: U19.124 (X0D31); also elsewhere on the board
/usb bridge/GP0_8C_6: U19.123 (X0D32); also elsewhere on the board
/usb bridge/GP0_8C_7: U19.126 (X0D33); also elsewhere on the board
/usb bridge/GP0_8D_0: R94.2, U18.7 (SDA/OUT1), U19.94 (X0D36)
/usb bridge/GP0_8D_1: U19.96 (X0D37); also elsewhere on the board
/usb bridge/GP0_8D_2: U19.97 (X0D38)
/usb bridge/GP0_8D_3: U19.99 (X0D39); also elsewhere on the board
/usb bridge/GP0_8D_4: U19.98 (X0D40); also elsewhere on the board
/usb bridge/GP0_8D_5: U19.101 (X0D41); also elsewhere on the board
/usb bridge/GP0_8D_6: U19.100 (X0D42); also elsewhere on the board
/usb bridge/GP0_8D_7: U19.103 (X0D43); also elsewhere on the board
/usb bridge/GP1_1A: U19.19 (X1D00); also elsewhere on the board
/usb bridge/GP1_1B: U19.20 (X1D01); also elsewhere on the board
/usb bridge/GP1_1C: U19.22 (X1D10); also elsewhere on the board
/usb bridge/GP1_1D: U19.23 (X1D11); also elsewhere on the board
/usb bridge/GP1_1F: U19.64 (X1D13); also elsewhere on the board
/usb bridge/GP1_1G: U19.74 (X1D22); also elsewhere on the board
/usb bridge/GP1_1I: U19.107 (X1D24); also elsewhere on the board
/usb bridge/GP1_1J: U19.108 (X1D25); also elsewhere on the board
/usb bridge/GP1_1K: U19.119 (X1D34); also elsewhere on the board
/usb bridge/GP1_1L: U19.120 (X1D35); also elsewhere on the board
/usb bridge/GP1_1M: U19.12 (X1D36); also elsewhere on the board
/usb bridge/GP1_1N: U19.13 (X1D37); also elsewhere on the board
/usb bridge/GP1_1O: U19.15 (X1D38); also elsewhere on the board
/usb bridge/GP1_1P: U19.16 (X1D39)
/usb bridge/GP1_4A_3: U19.21 (X1D09)
/usb bridge/GP1_4C_0: U19.63 (X1D14)
/usb bridge/GP1_4C_1: U19.65 (X1D15)
/usb bridge/GP1_4C_2: U19.71 (X1D20)
/usb bridge/GP1_4C_3: U19.73 (X1D21)
/usb bridge/GP1_4E_0: U19.110 (X1D26)
/usb bridge/GP1_4E_1: U19.111 (X1D27)
/usb bridge/GP1_4E_2: U19.117 (X1D32)
/usb bridge/GP1_4E_3: U19.118 (X1D33)
/usb bridge/GP1_4F_0: U19.112 (X1D28)
/usb bridge/GP1_4F_1: U19.114 (X1D29)
/usb bridge/GP1_4F_2: U19.115 (X1D30)
/usb bridge/GP1_4F_3: U19.116 (X1D31)
/usb bridge/GP1_8D_7: U19.102 (X1D43)
/usb bridge/GP1_32A_0: U19.75 (X1D49)
/usb bridge/GP1_32A_1: U19.76 (X1D50)
/usb bridge/GP1_32A_2: U19.77 (X1D51)
/usb bridge/GP1_32A_3: U19.78 (X1D52)
/usb bridge/GP1_32A_4: U19.79 (X1D53)
/usb bridge/GP1_32A_5: U19.80 (X1D54)
/usb bridge/GP1_32A_6: U19.81 (X1D55)
/usb bridge/GP1_32A_7: U19.82 (X1D56)
/usb bridge/GP1_32A_8: U19.83 (X1D57)
/usb bridge/GP1_32A_9: U19.84 (X1D58)
/usb bridge/IOB_GP0_1E: R93.2, R97.1, U19.46 (X0D12)
/usb bridge/IOB_GP0_1F: U19.47 (X0D13)
/usb bridge/IOB_GP0_1G: U19.48 (X0D22)
/usb bridge/IOB_GP0_1H: U19.49 (X0D23)
/usb bridge/IOB_GP1_1E: U19.53 (X1D12)
/usb bridge/IOB_GP1_1H: U19.57 (X1D23)
/usb bridge/JTAG_TCK: J6.4, U19.51 (TCK)
/usb bridge/JTAG_TDI: J6.8, U19.36 (TDI)
/usb bridge/JTAG_TDO: J6.6, U19.37 (TDO)
/usb bridge/JTAG_TMS: J6.2, U19.44 (TMS)
/usb bridge/PLL_AVDD: C152.1, FB1.1, U19.41 (PLL_AVDD)
/usb bridge/QSPI_CS: R92.2, U17.1 (~CS), U19.2 (X0D01)
/usb bridge/QSPI_SCLK: U17.6 (CLK), U19.4 (X0D10)
/usb bridge/QSPI_SPIO0: U17.5 (DI/IO_{0}), U19.127 (X0D04)
/usb bridge/QSPI_SPIO1: U17.2 (DO/IO_{1}), U19.128 (X0D05)
/usb bridge/QSPI_SPIO2: U17.3 (~WP/IO_{2}), U19.1 (X0D06)
/usb bridge/QSPI_SPIO3: U17.7 (~HOLD/~RESET/IO_{3}), U19.3 (X0D07)
/usb bridge/RST_N: J6.10, U19.38 (~RST)
/usb bridge/VBUS: C150.1, C151.2, J7.A4 (VBUS), J7.A9 (VBUS), J7.B4 (VBUS), J7.B9 (VBUS), R93.1, R96.1, U18.4 (VBUS_DET); also elsewhere on the board
/usb bridge/XL0_IN_0: J6.14, U19.67 (X1D17)
/usb bridge/XL0_IN_1: J6.12, U19.66 (X1D16)
/usb bridge/XL0_OUT_0: J6.16, U19.69 (X1D18)
/usb bridge/XL0_OUT_1: J6.18, U19.70 (X1D19)
Earth: C125.2, C126.2, C127.2, C128.2, C129.2, C130.2, C131.2, C132.2, C133.2, C134.2, C135.2, C136.2, C137.2, C138.2, C139.2, C140.2, C141.2, C142.2, C143.2, C144.2, C145.2, C146.2, C147.2, C148.2, C149.2, C150.2, C151.1, C152.2, C153.2, C154.2, C155.1, C156.1, J6.3, J6.5, J6.7, J6.9, J6.13, J6.15, J6.17, J6.19, J7.A1 (GND), J7.A12 (GND), J7.B1 (GND), J7.B12 (GND), R96.2, R97.2, U16.7 (GND), U17.4 (GND), U18.3 (PORT), U18.10 (GND), U19.24 (MIPI_VDD18), U19.27 (MIPI_VDD09), U19.30 (VSS), U19.42 (PLL_AGND), U19.129 (VSS__1), Y1.2 (G), Y1.4 (G); also elsewhere on the board
unnamed: C155.2, R102.1, Y1.3
unnamed: J6.20, R95.2
unnamed: C156.2, R101.2, U19.34 (XIN), Y1.1
unnamed: R101.1, R102.2, U19.33 (XOUT)
unnamed: J7.A7 (D-), J7.B7 (D-), U19.59 (USB_DM)
unnamed: J7.A6 (D+), J7.B6 (D+), U19.60 (USB_DP)

Notes on the sheet:
leave floating for 3V3

Board: 2 copper layers, 432 parts (0 on the bottom side), 280 nets, no tracks yet.
